norbert-walter/LoRa-Boat-Monitor/project/apps/pictures/Bonjour_Browser.png

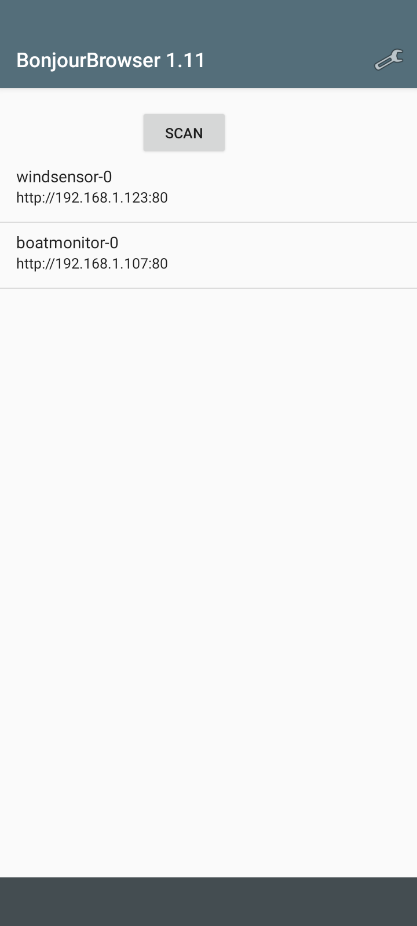
project/apps/pictures/Bonjour_Browser.png
