norbert-walter/LoRa-Boat-Monitor/project/apps/pictures/Lora_Info.png

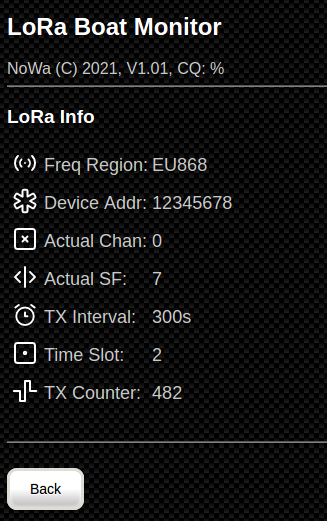
project/apps/pictures/Lora_Info.png
