norbert-walter/LoRa-Boat-Monitor/project/apps/pictures/Menue.png

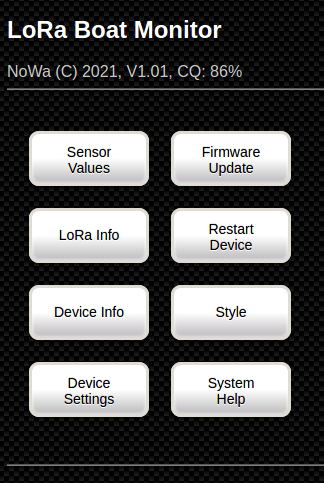
project/apps/pictures/Menue.png
