norbert-walter/LoRa-Boat-Monitor/project/apps/pictures/Screenshot_1.png

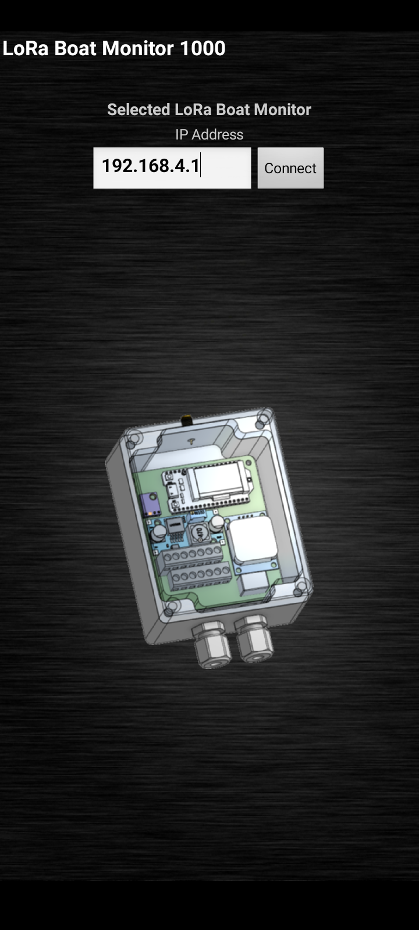
project/apps/pictures/Screenshot_1.png
