norbert-walter/LoRa-Boat-Monitor/project/apps/pictures/Screenshot_2.png

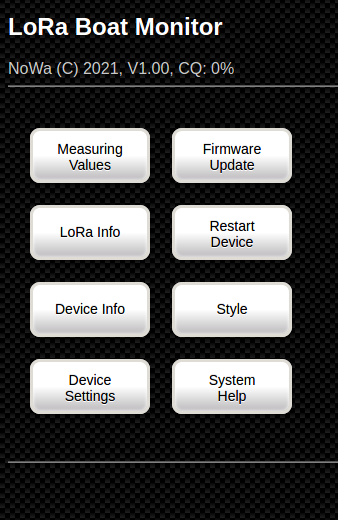
project/apps/pictures/Screenshot_2.png
