norbert-walter/LoRa-Boat-Monitor/project/apps/pictures/Sensor_Values1.png

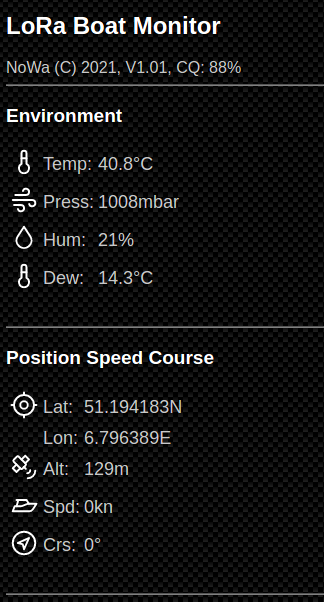
project/apps/pictures/Sensor_Values1.png
