norbert-walter/LoRa-Boat-Monitor/project/apps/pictures/Sensor_Values2.png

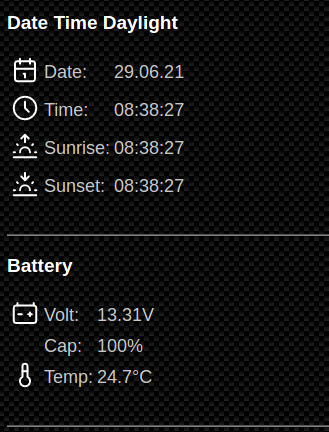
project/apps/pictures/Sensor_Values2.png
