norbert-walter/LoRa-Boat-Monitor/project/apps/pictures/Sensor_Values3.png

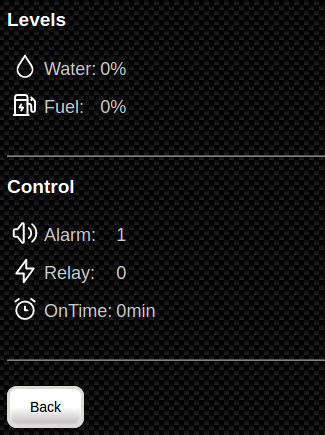
project/apps/pictures/Sensor_Values3.png
