norbert-walter/LoRa-Boat-Monitor/project/docs/Certifications/Heltec_LoRa32/464_Smith.png

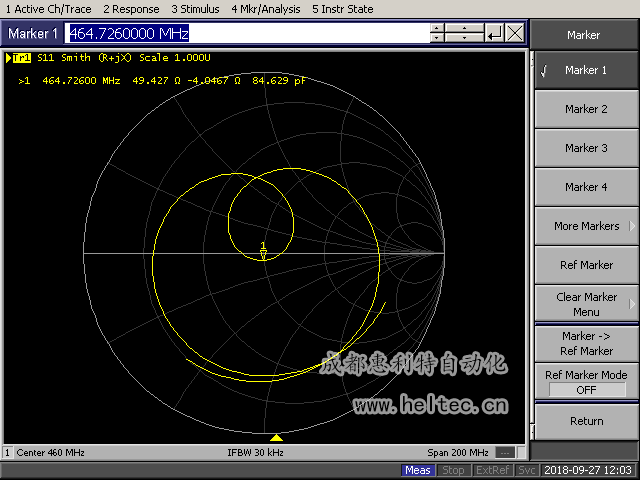
project/docs/Certifications/Heltec_LoRa32/464_Smith.png
