norbert-walter/LoRa-Boat-Monitor/project/docs/Certifications/Heltec_LoRa32/lite470.png

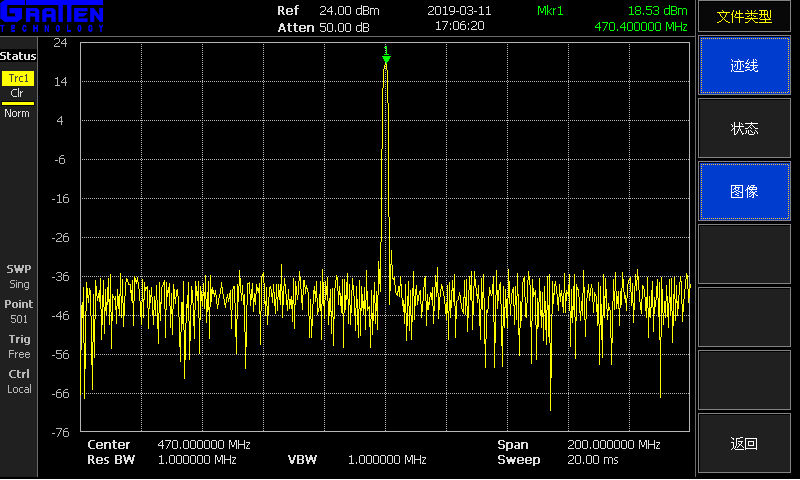
project/docs/Certifications/Heltec_LoRa32/lite470.png
