norbert-walter/LoRa-Boat-Monitor/project/docs/Certifications/Heltec_LoRa32/lite826.png

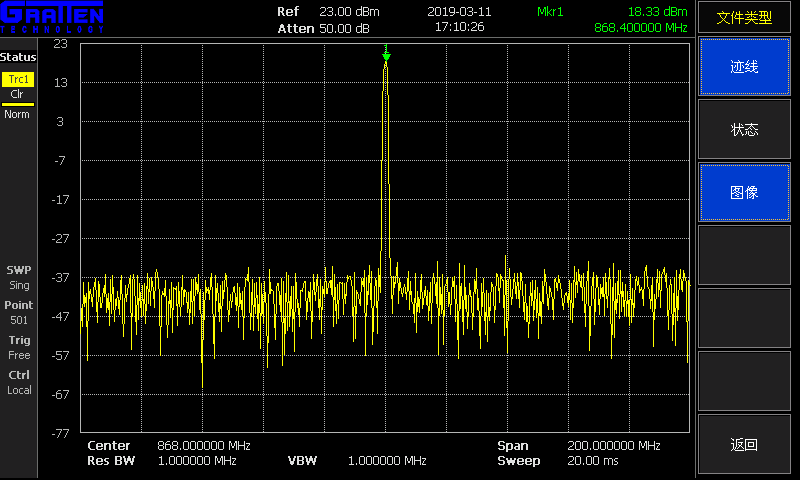
project/docs/Certifications/Heltec_LoRa32/lite826.png
