norbert-walter/LoRa-Boat-Monitor/project/docs/Certifications/Heltec_LoRa32/lite915.png

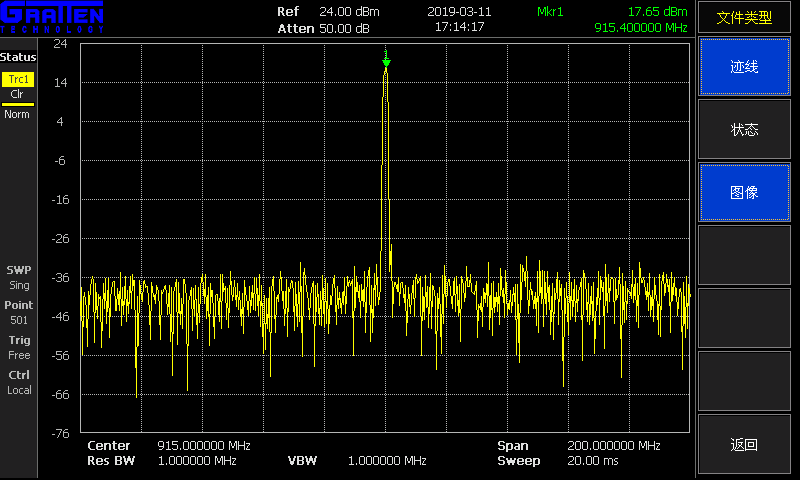
project/docs/Certifications/Heltec_LoRa32/lite915.png
