norbert-walter/LoRa-Boat-Monitor/project/docs/Componets/Heltec_WiFi_LoRa_32.png

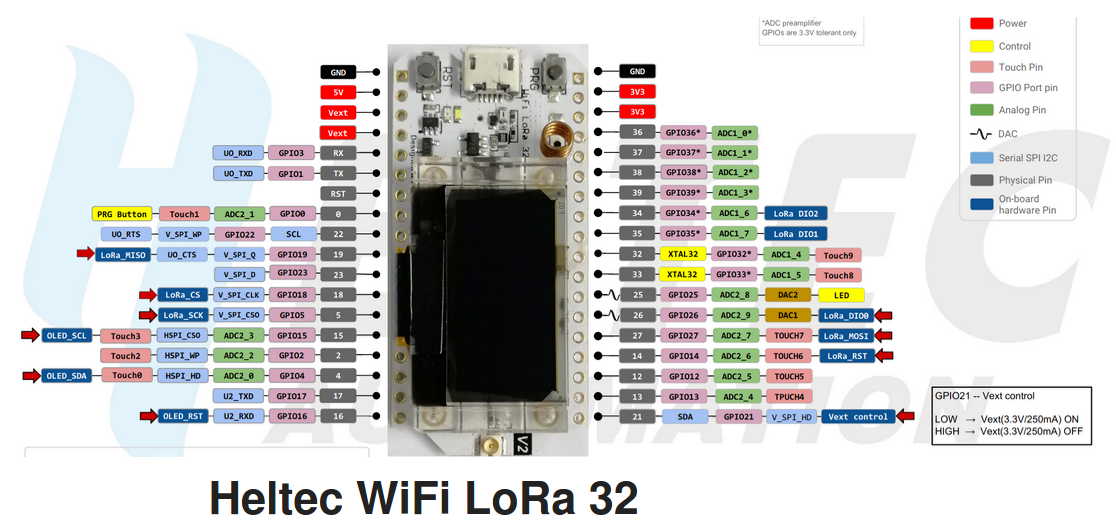
project/docs/Componets/Heltec_WiFi_LoRa_32.png
