norbert-walter/LoRa-Boat-Monitor/project/pictures/LoRa_Boat_Monitor/Füllstandssensor_180_Ohm.jpg

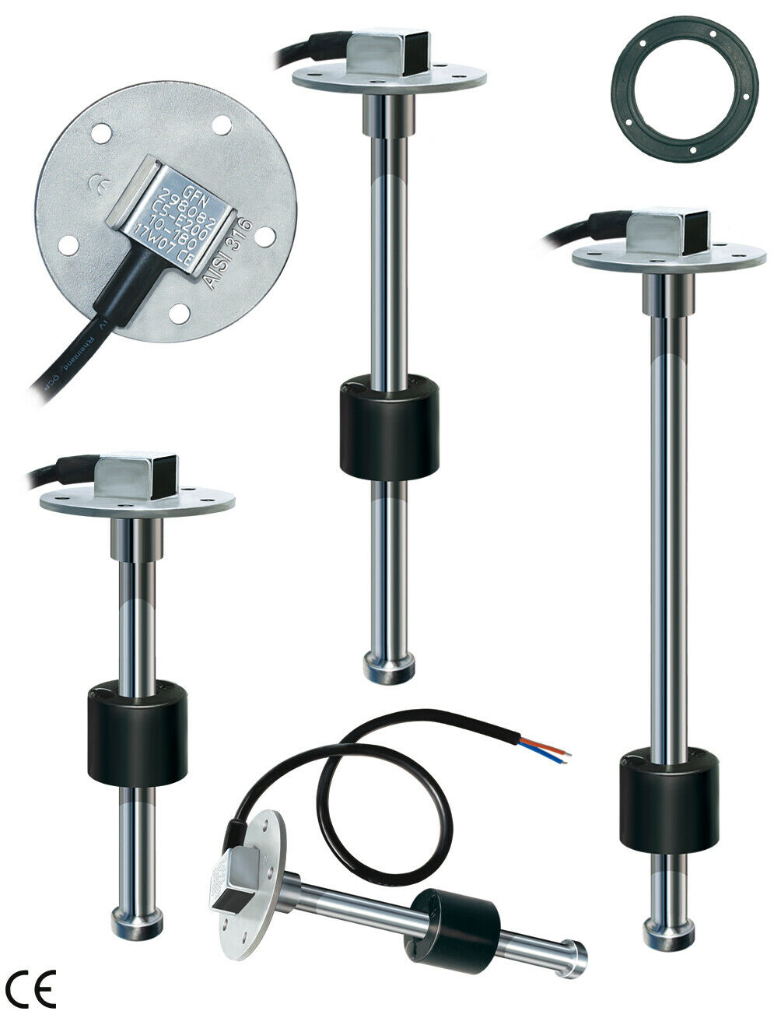
project/pictures/LoRa_Boat_Monitor/Füllstandssensor_180_Ohm.jpg
