norbert-walter/LoRa-Boat-Monitor/project/pictures/LoRa_Boat_Monitor/IMG_20200325_182847_kl.jpg

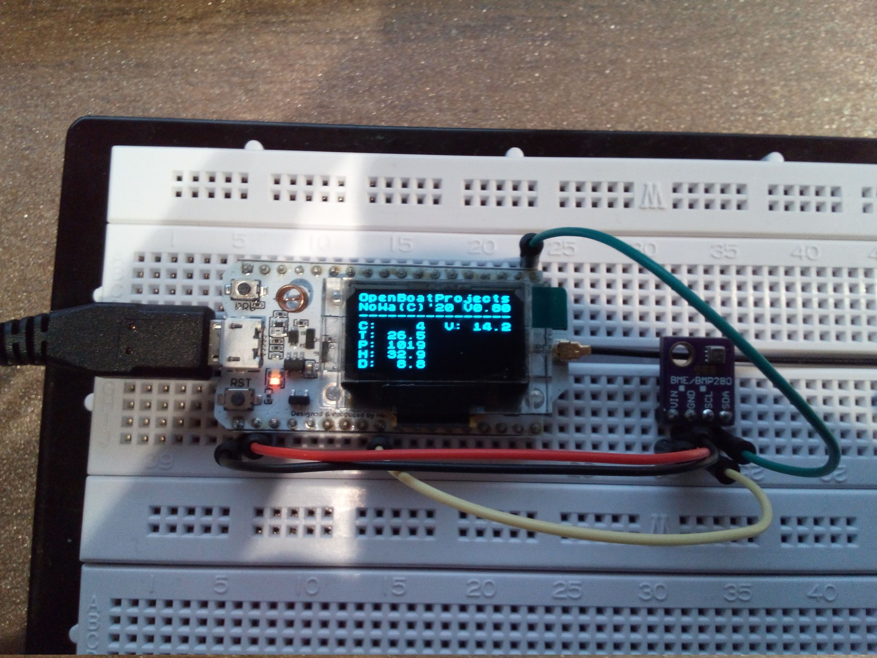
project/pictures/LoRa_Boat_Monitor/IMG_20200325_182847_kl.jpg
