norbert-walter/LoRa-Boat-Monitor/project/pictures/LoRa_Boat_Monitor/IMG_20200403_091831_kl.jpg

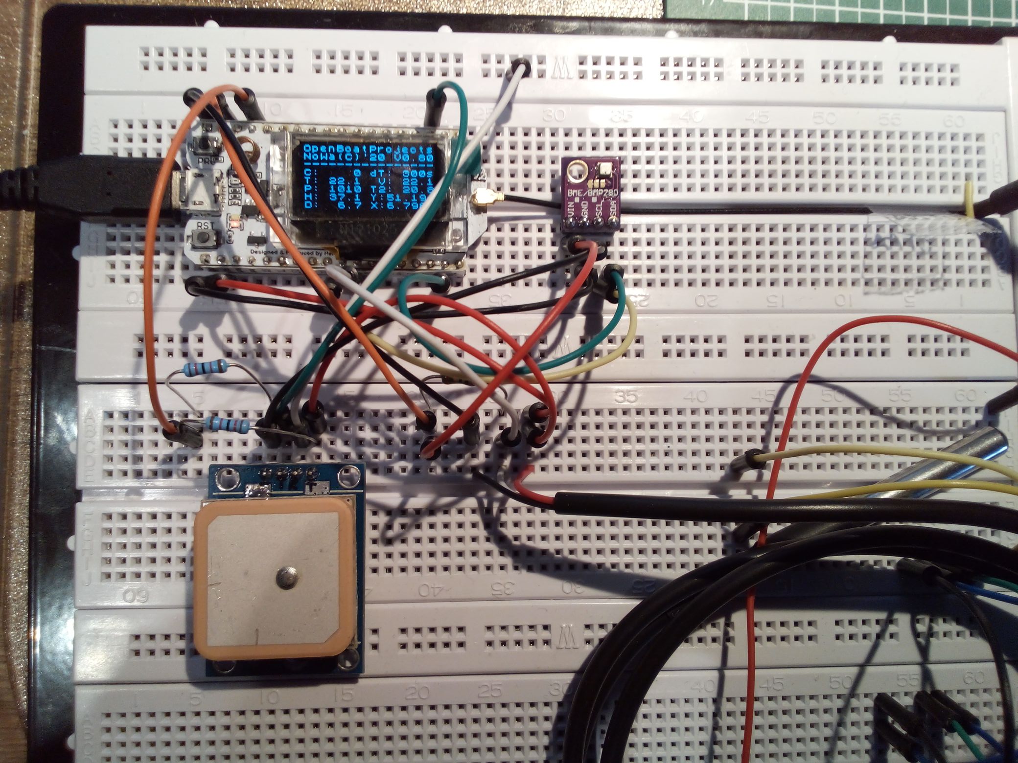
project/pictures/LoRa_Boat_Monitor/IMG_20200403_091831_kl.jpg
