norbert-walter/LoRa-Boat-Monitor/project/pictures/LoRa_Boat_Monitor/IMG_20200506_172737_kl.jpg

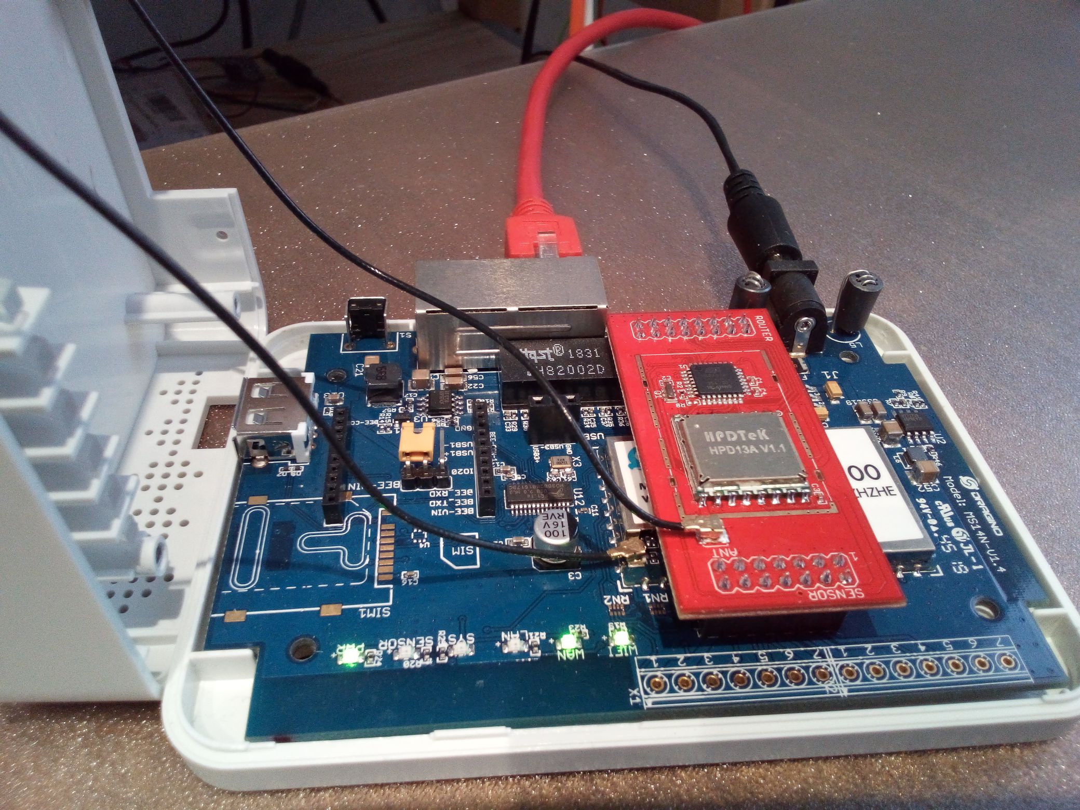
project/pictures/LoRa_Boat_Monitor/IMG_20200506_172737_kl.jpg
