norbert-walter/LoRa-Boat-Monitor/project/pictures/LoRa_Boat_Monitor/IMG_20200603_171321_kl.jpg

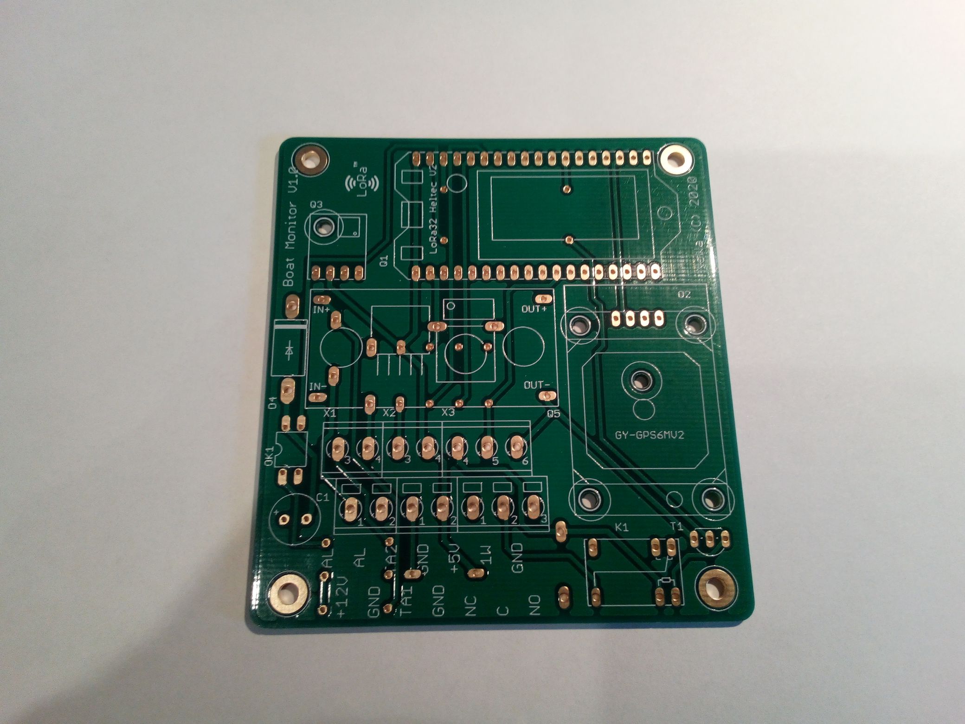
project/pictures/LoRa_Boat_Monitor/IMG_20200603_171321_kl.jpg
