norbert-walter/LoRa-Boat-Monitor/project/pictures/LoRa_Boat_Monitor/IMG_20200603_210354_kl.jpg

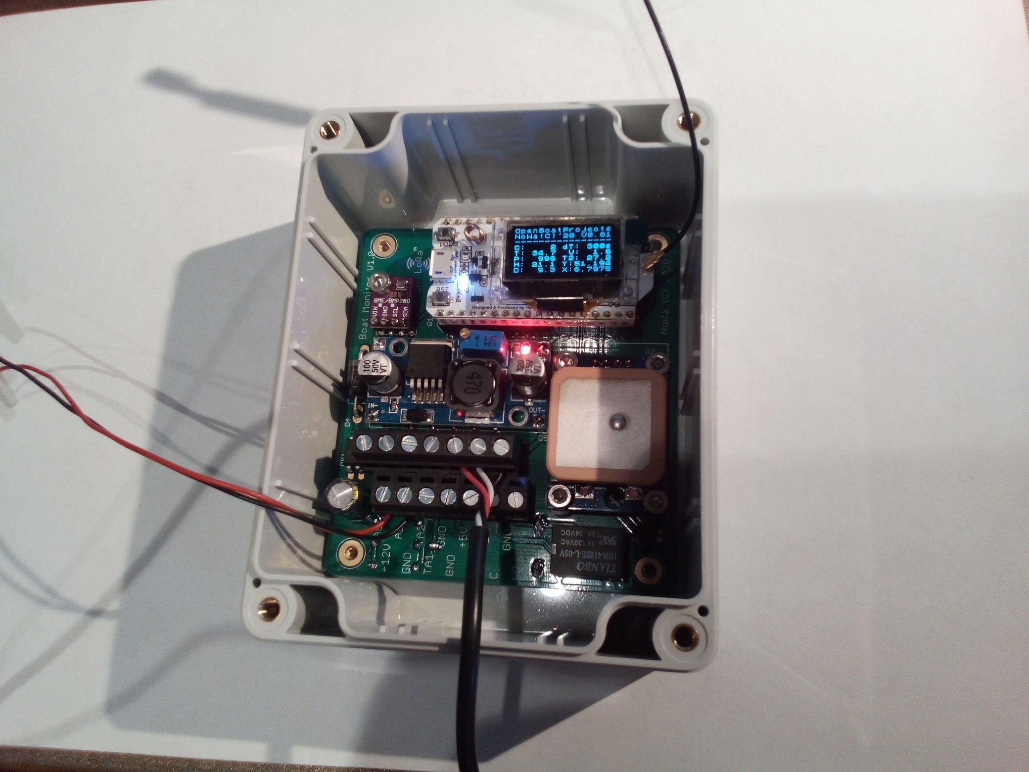
project/pictures/LoRa_Boat_Monitor/IMG_20200603_210354_kl.jpg
