norbert-walter/LoRa-Boat-Monitor/project/pictures/LoRa_Boat_Monitor/IMG_20200605_140513_kl.jpg

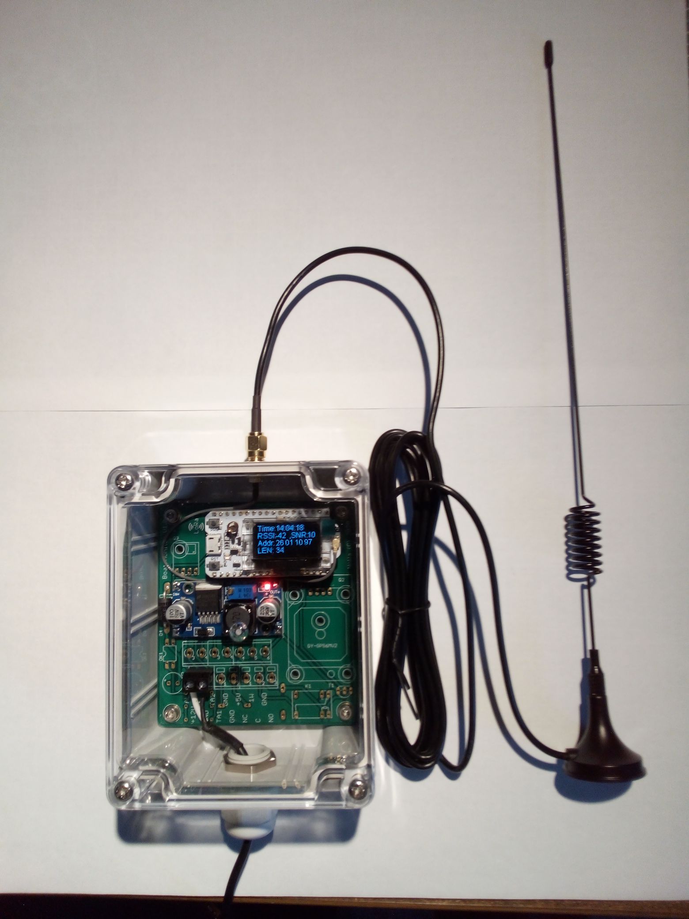
project/pictures/LoRa_Boat_Monitor/IMG_20200605_140513_kl.jpg
