norbert-walter/LoRa-Boat-Monitor/project/pictures/LoRa_Boat_Monitor/IMG_20201030_144952_kl.jpg

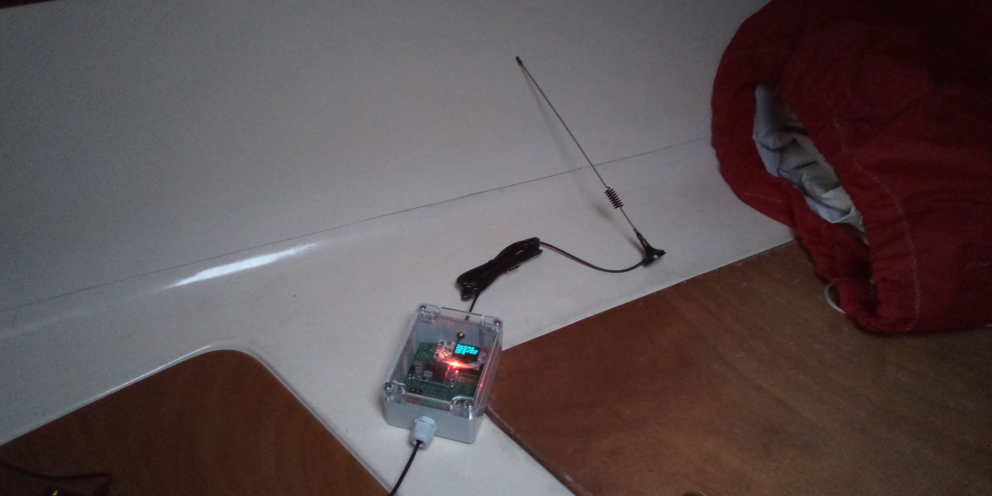
project/pictures/LoRa_Boat_Monitor/IMG_20201030_144952_kl.jpg
