norbert-walter/LoRa-Boat-Monitor/project/pictures/LoRa_Boat_Monitor/IMG_20210512_152236_kl.jpg

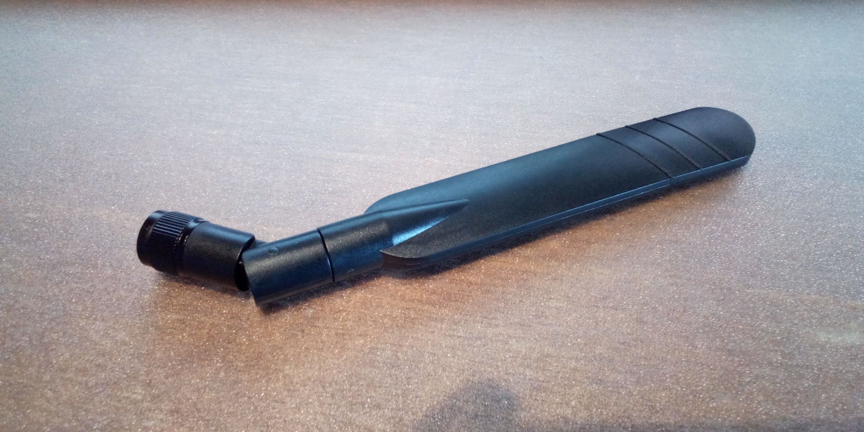
project/pictures/LoRa_Boat_Monitor/IMG_20210512_152236_kl.jpg
