norbert-walter/LoRa-Boat-Monitor/project/pictures/LoRa_Boat_Monitor/IMG_20210512_152258_kl.jpg

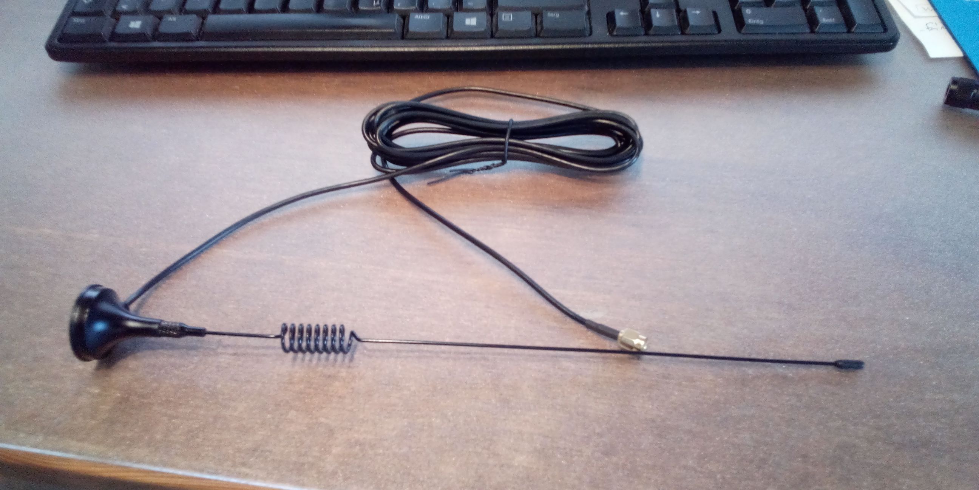
project/pictures/LoRa_Boat_Monitor/IMG_20210512_152258_kl.jpg
