norbert-walter/LoRa-Boat-Monitor/project/pictures/LoRa_Boat_Monitor/LoRa-Frequenz-und-Signalstärke_klein_klein.jpg

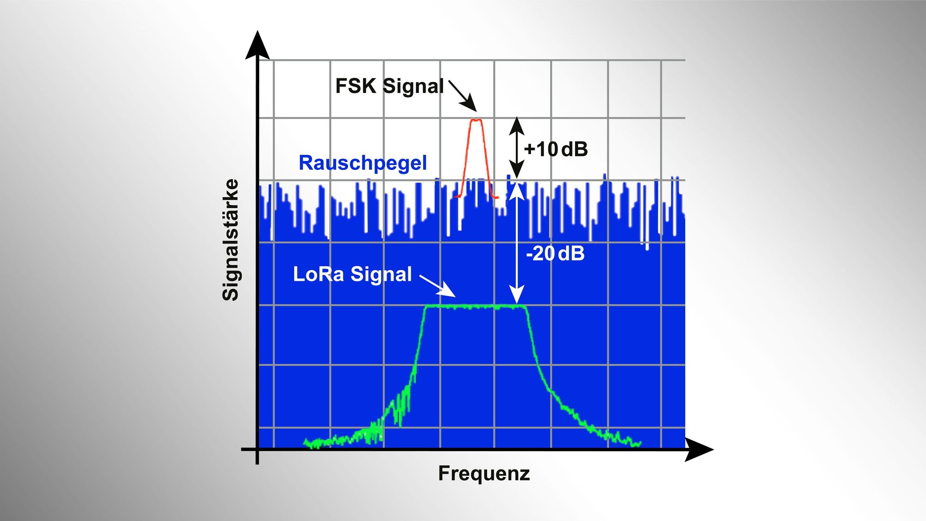
project/pictures/LoRa_Boat_Monitor/LoRa-Frequenz-und-Signalstärke_klein_klein.jpg
