norbert-walter/LoRa-Boat-Monitor/project/pictures/LoRa_Boat_Monitor/LoRa_Boatmonitor_Case.png

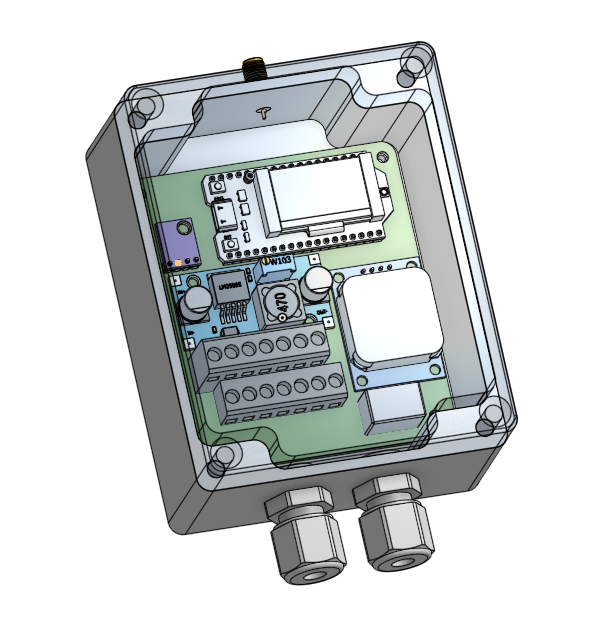
project/pictures/LoRa_Boat_Monitor/LoRa_Boatmonitor_Case.png
