norbert-walter/LoRa-Boat-Monitor/project/pictures/LoRa_Boat_Monitor/LoRa_Boots_Monitor_2.png

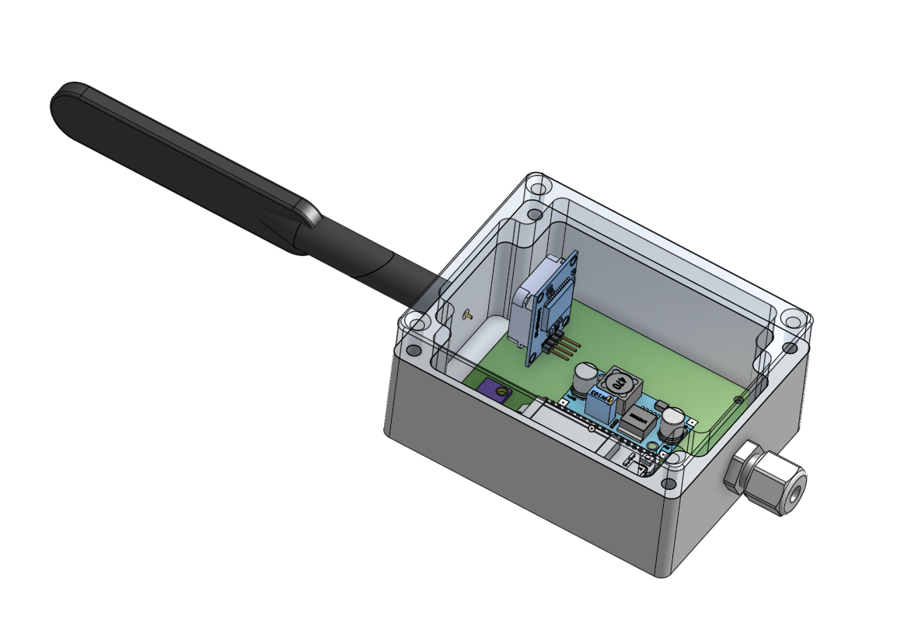
project/pictures/LoRa_Boat_Monitor/LoRa_Boots_Monitor_2.png
