norbert-walter/LoRa-Boat-Monitor/project/pictures/LoRa_Boat_Monitor/LoRa_Bootsmonitor.png

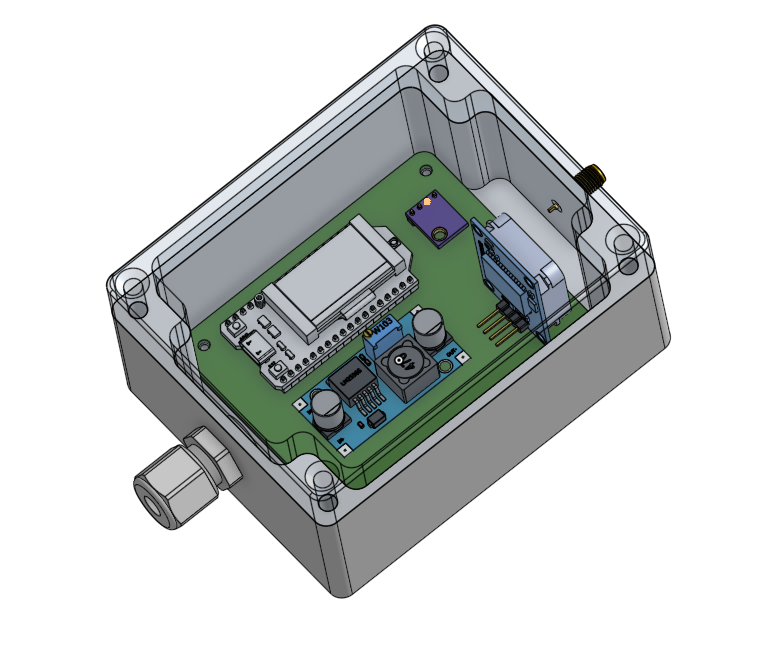
project/pictures/LoRa_Boat_Monitor/LoRa_Bootsmonitor.png
