norbert-walter/LoRa-Boat-Monitor/project/pictures/LoRa_Boat_Monitor/LoRa_Bootsmonitor_Bottom_2_kl.png

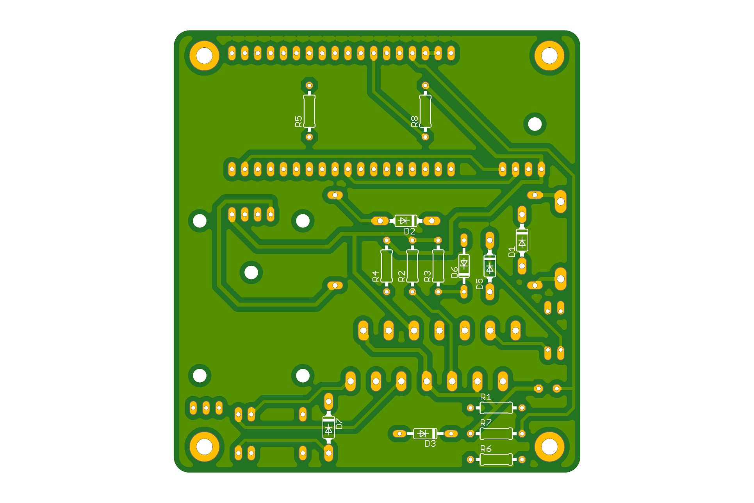
project/pictures/LoRa_Boat_Monitor/LoRa_Bootsmonitor_Bottom_2_kl.png
