norbert-walter/LoRa-Boat-Monitor/project/pictures/LoRa_Boat_Monitor/LoRa_Bootsmonitor_Top_2_kl.png

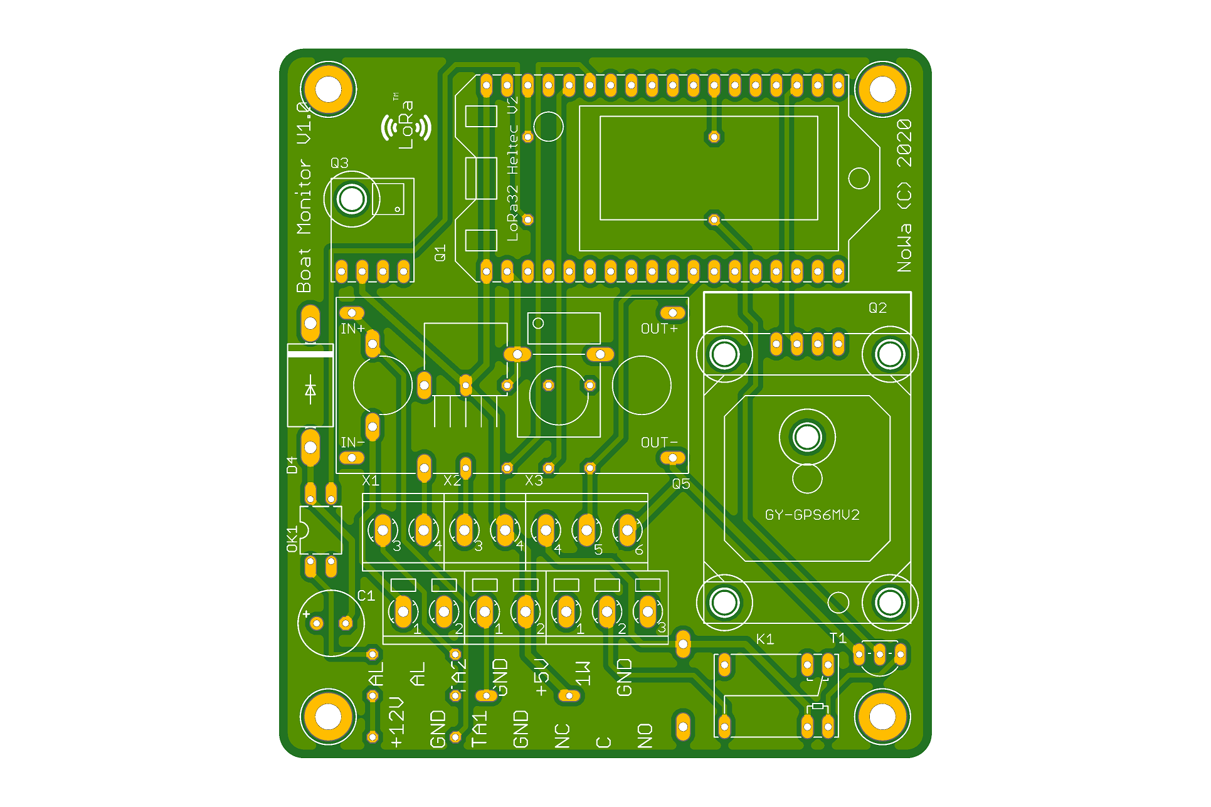
project/pictures/LoRa_Boat_Monitor/LoRa_Bootsmonitor_Top_2_kl.png
