norbert-walter/LoRa-Boat-Monitor/project/pictures/LoRa_Boat_Monitor/Schwimmschalter.jpg

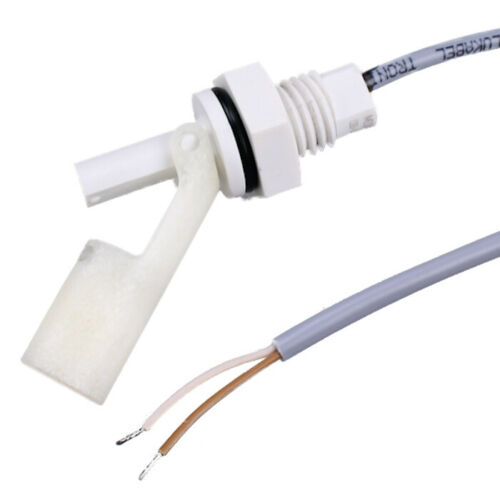
project/pictures/LoRa_Boat_Monitor/Schwimmschalter.jpg
