norbert-walter/LoRa-Boat-Monitor/project/pictures/LoRa_Boat_Monitor/Schwimmschalter_3.jpg

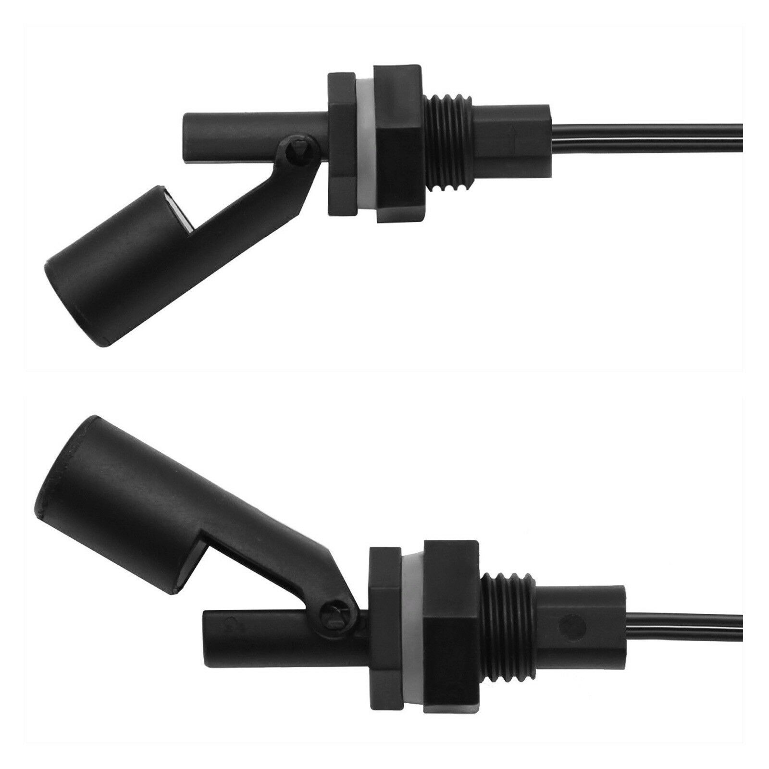
project/pictures/LoRa_Boat_Monitor/Schwimmschalter_3.jpg
