norbert-walter/LoRa-Boat-Monitor/project/pictures/LoRa_Boat_Monitor/Türschalter_magnetisch.jpg

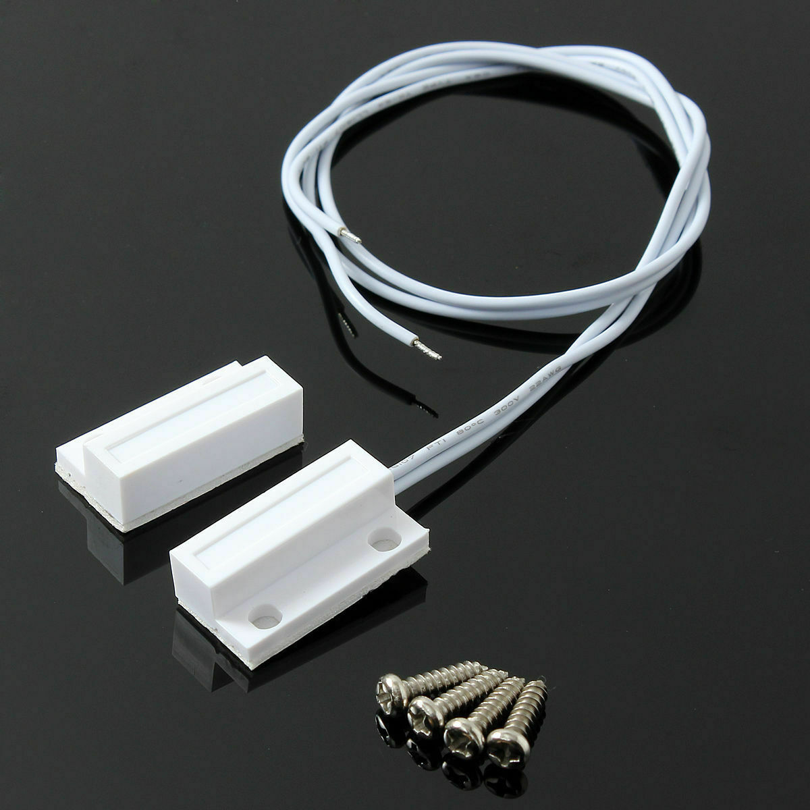
project/pictures/LoRa_Boat_Monitor/Türschalter_magnetisch.jpg
