norbert-walter/LoRa-Boat-Monitor/project/pictures/LoRa_Gateway/Dragino_LoRa_Gateway_LG01-P.png

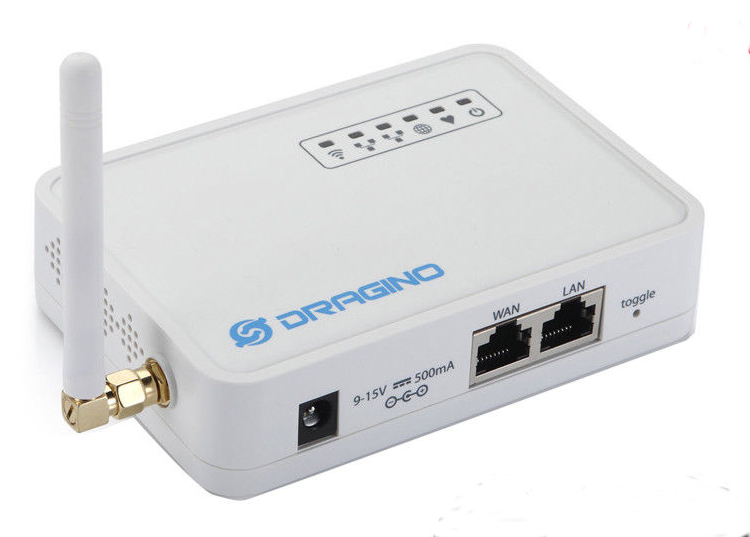
project/pictures/LoRa_Gateway/Dragino_LoRa_Gateway_LG01-P.png
