norbert-walter/LoRa-Boat-Monitor/project/pictures/LoRa_Gateway/LoRa_1Ch_Gateway.png

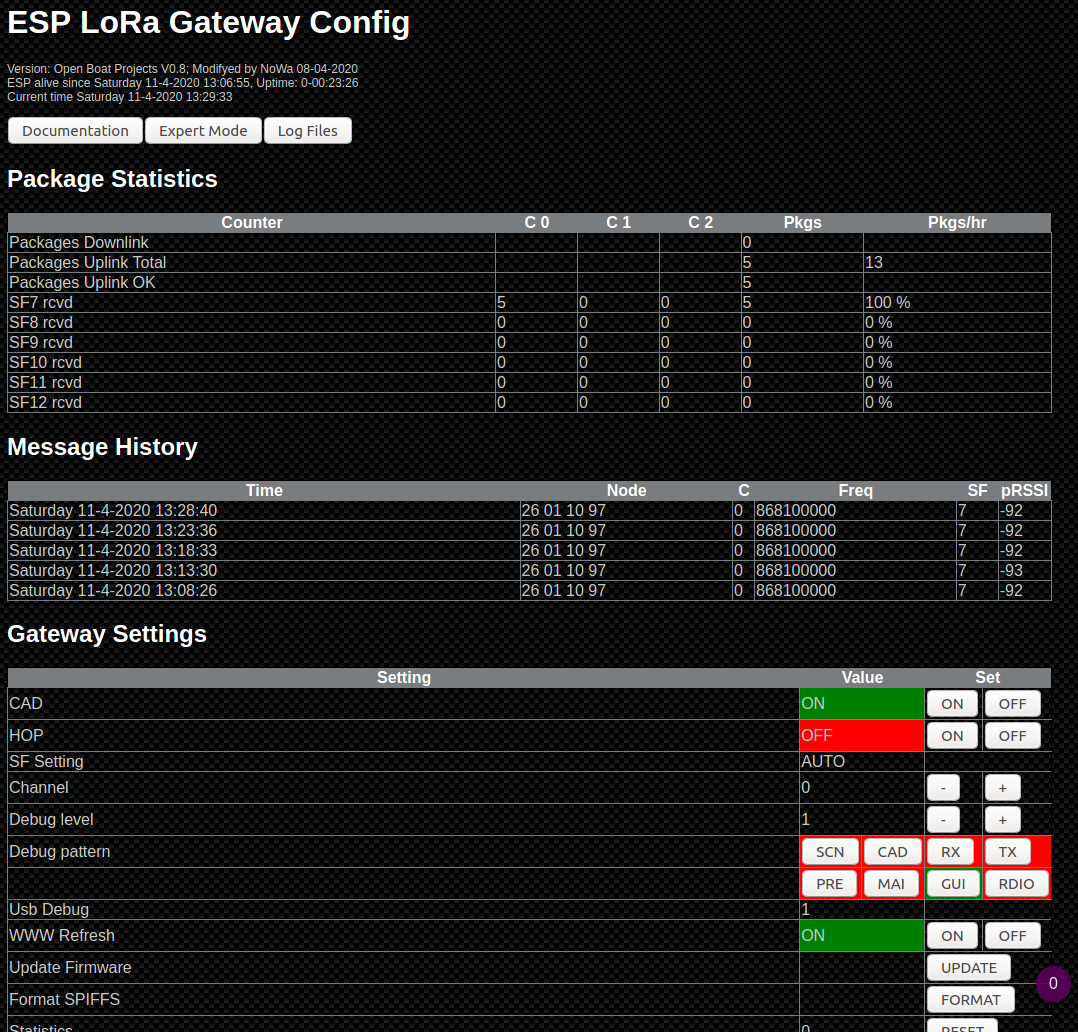
project/pictures/LoRa_Gateway/LoRa_1Ch_Gateway.png
