norbert-walter/LoRa-Boat-Monitor/project/pictures/LoRa_Gateway/LoRa_Gateway.png

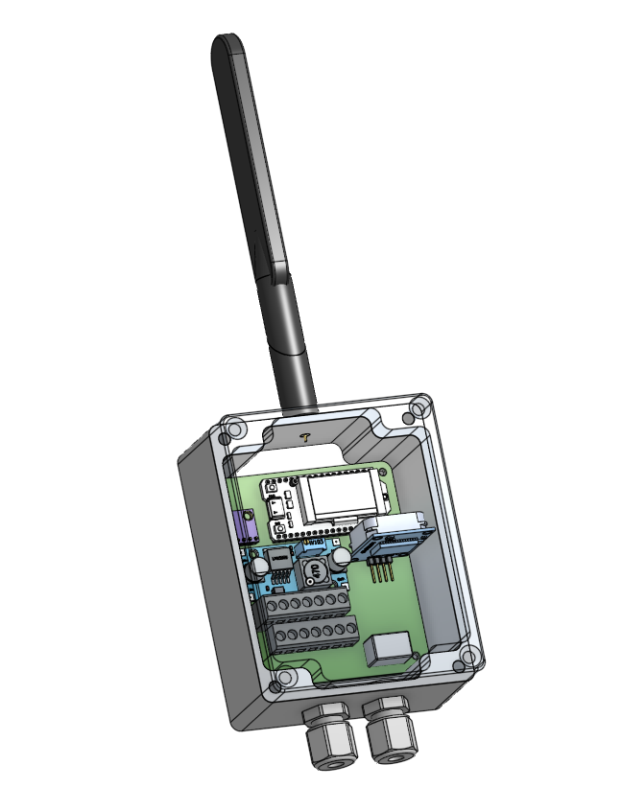
project/pictures/LoRa_Gateway/LoRa_Gateway.png
