norbert-walter/LoRa-Boat-Monitor/project/pictures/Sailboat_bl_or.png

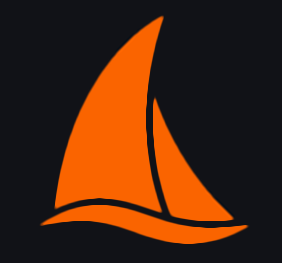
project/pictures/Sailboat_bl_or.png
