norbert-walter/LoRa-Boat-Monitor/project/pictures/TTN/Application_Data.png

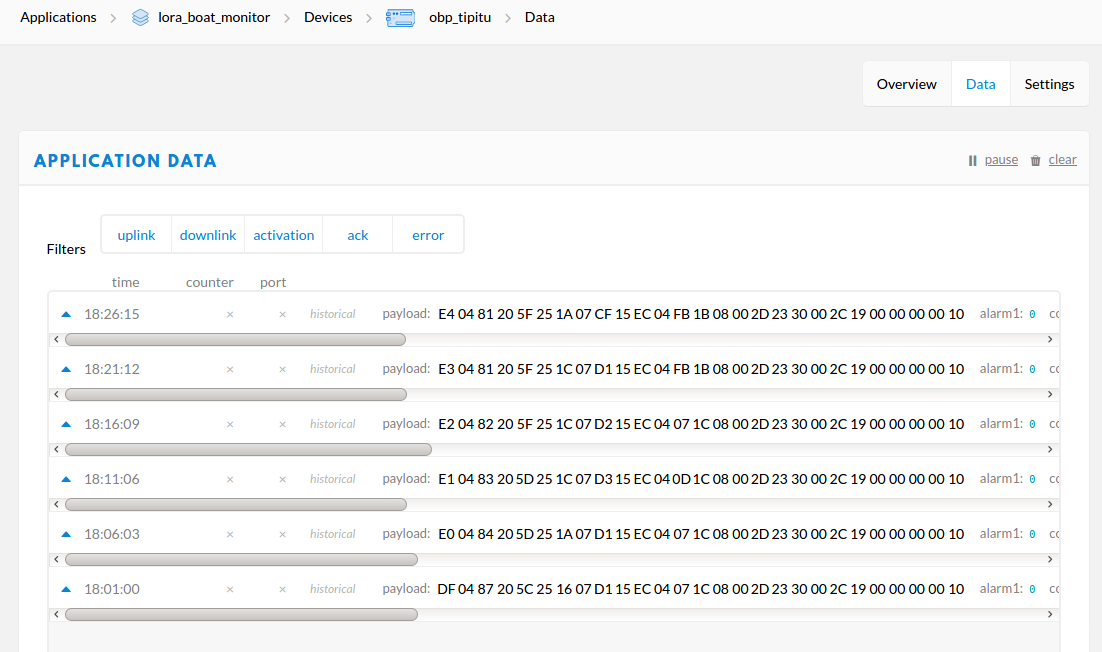
project/pictures/TTN/Application_Data.png
