norbert-walter/LoRa-Boat-Monitor/project/pictures/TTN/Metadata.png

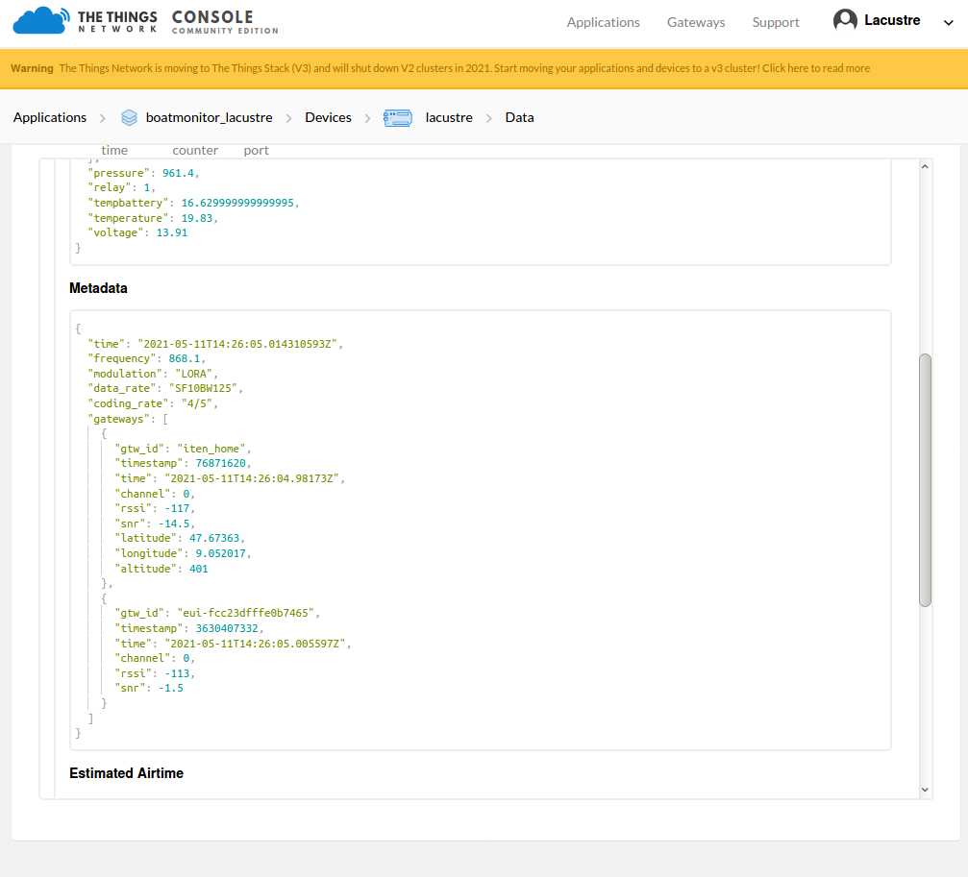
project/pictures/TTN/Metadata.png
