norbert-walter/LoRa-Boat-Monitor/project/pictures/TTN/Upload_Bestaetigung2.png

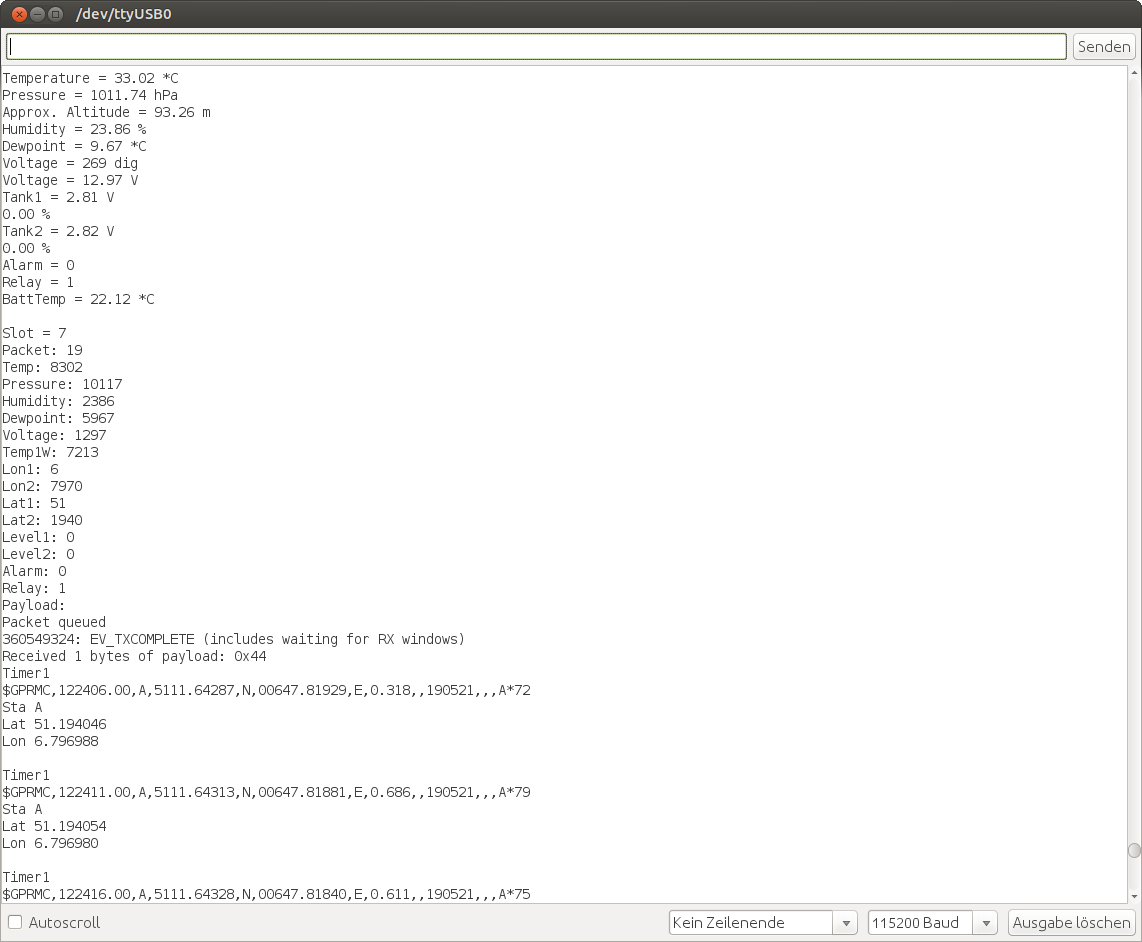
project/pictures/TTN/Upload_Bestaetigung2.png
