norbert-walter/LoRa-Boat-Monitor/project/pictures/TTN/Upload_Bestaetigung.png

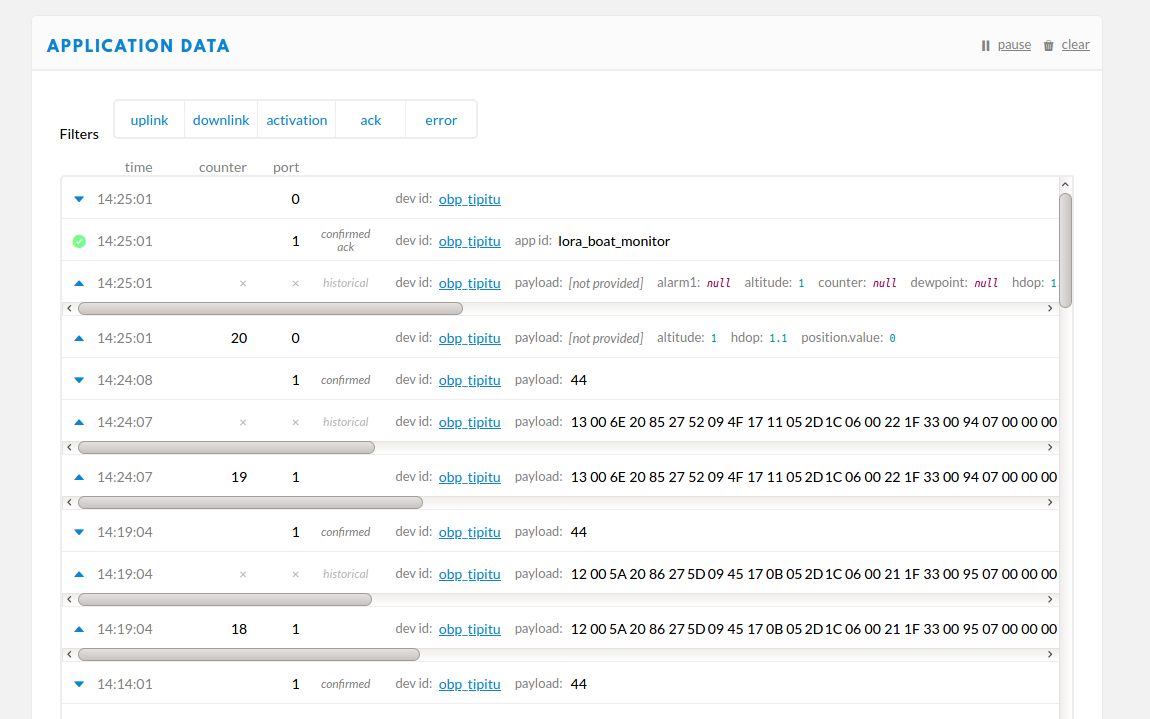
project/pictures/TTN/Upload_Bestaetigung.png
