norbert-walter/LoRa-Boat-Monitor/project/pictures/Ubidots/LoRa_Monitoring_Karte.png

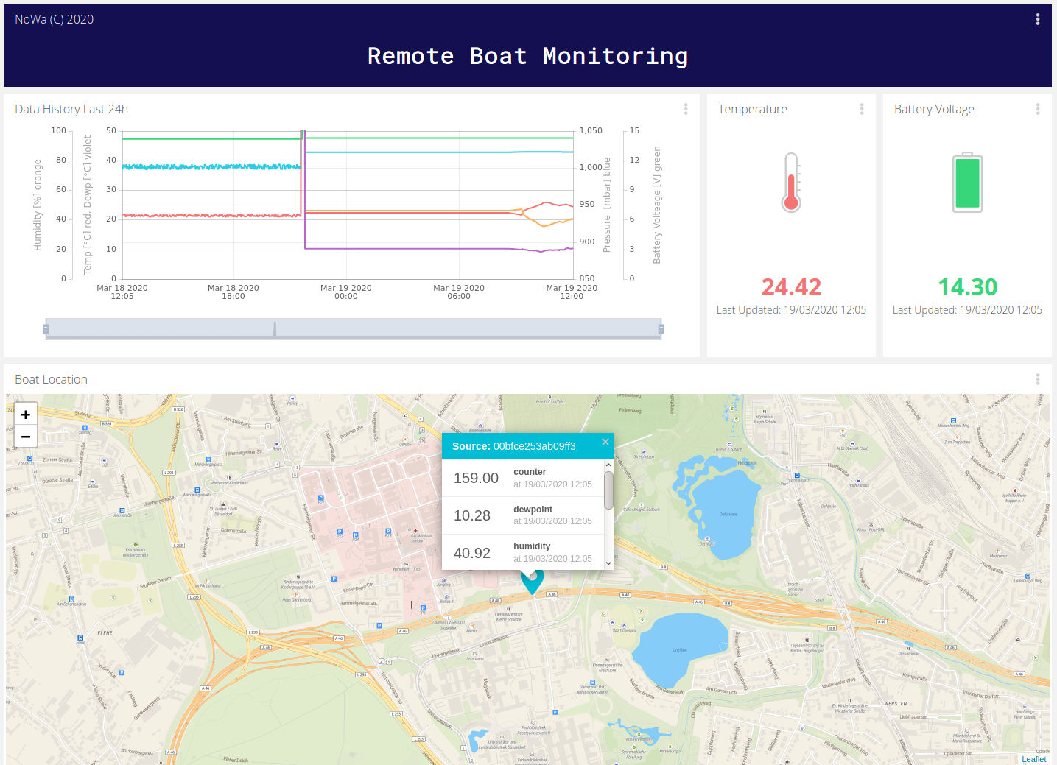
project/pictures/Ubidots/LoRa_Monitoring_Karte.png
