norbert-walter/LoRa-Boat-Monitor/project/pictures/Ubidots/SY-Balder Messdaten2.png

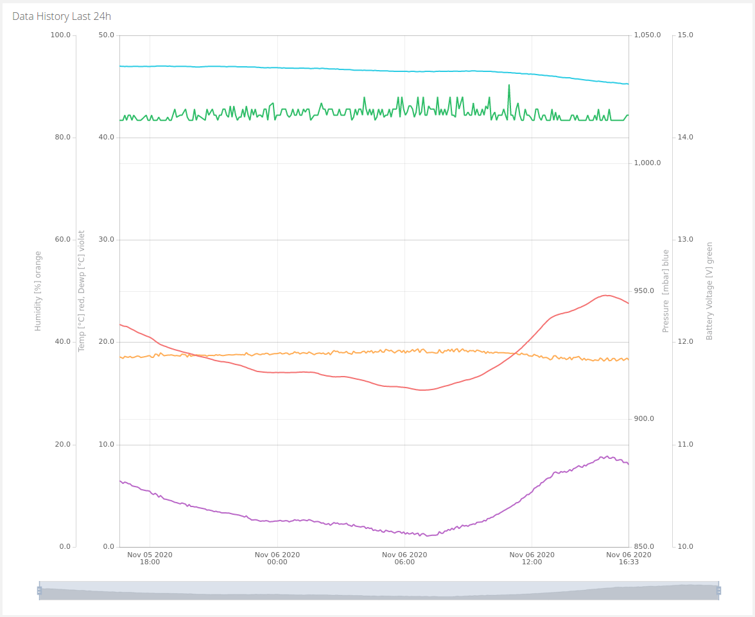
project/pictures/Ubidots/SY-Balder Messdaten2.png
