norbert-walter/LoRa-Boat-Monitor/project/pictures/Ubidots/SY-Balder_Messdaten.png

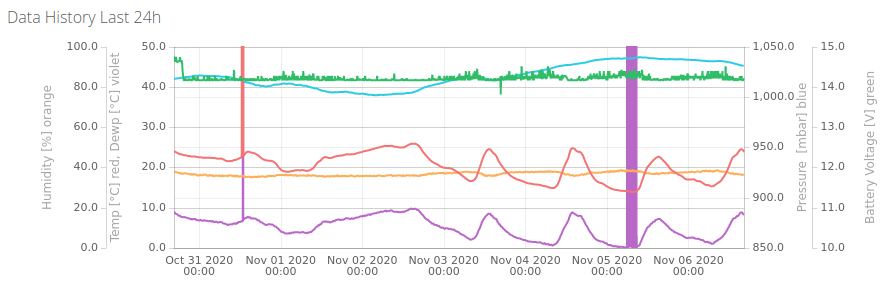
project/pictures/Ubidots/SY-Balder_Messdaten.png
