norbert-walter/LoRa-Boat-Monitor/project/pictures/Ubidots/Ubidots_24h_Verbindungsqualitaet.png

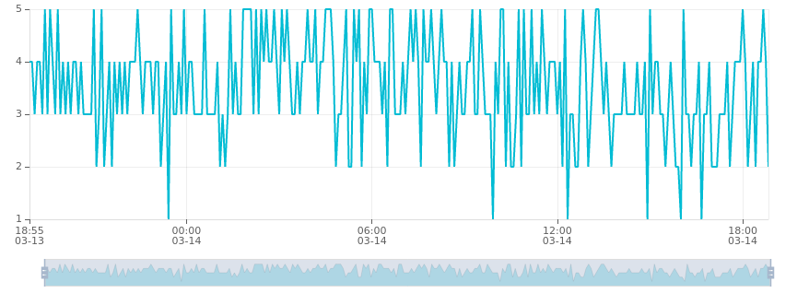
project/pictures/Ubidots/Ubidots_24h_Verbindungsqualitaet.png
