norbert-walter/LoRa-Boat-Monitor/project/pictures/Antenna_Characteristic/Knickantenne.png

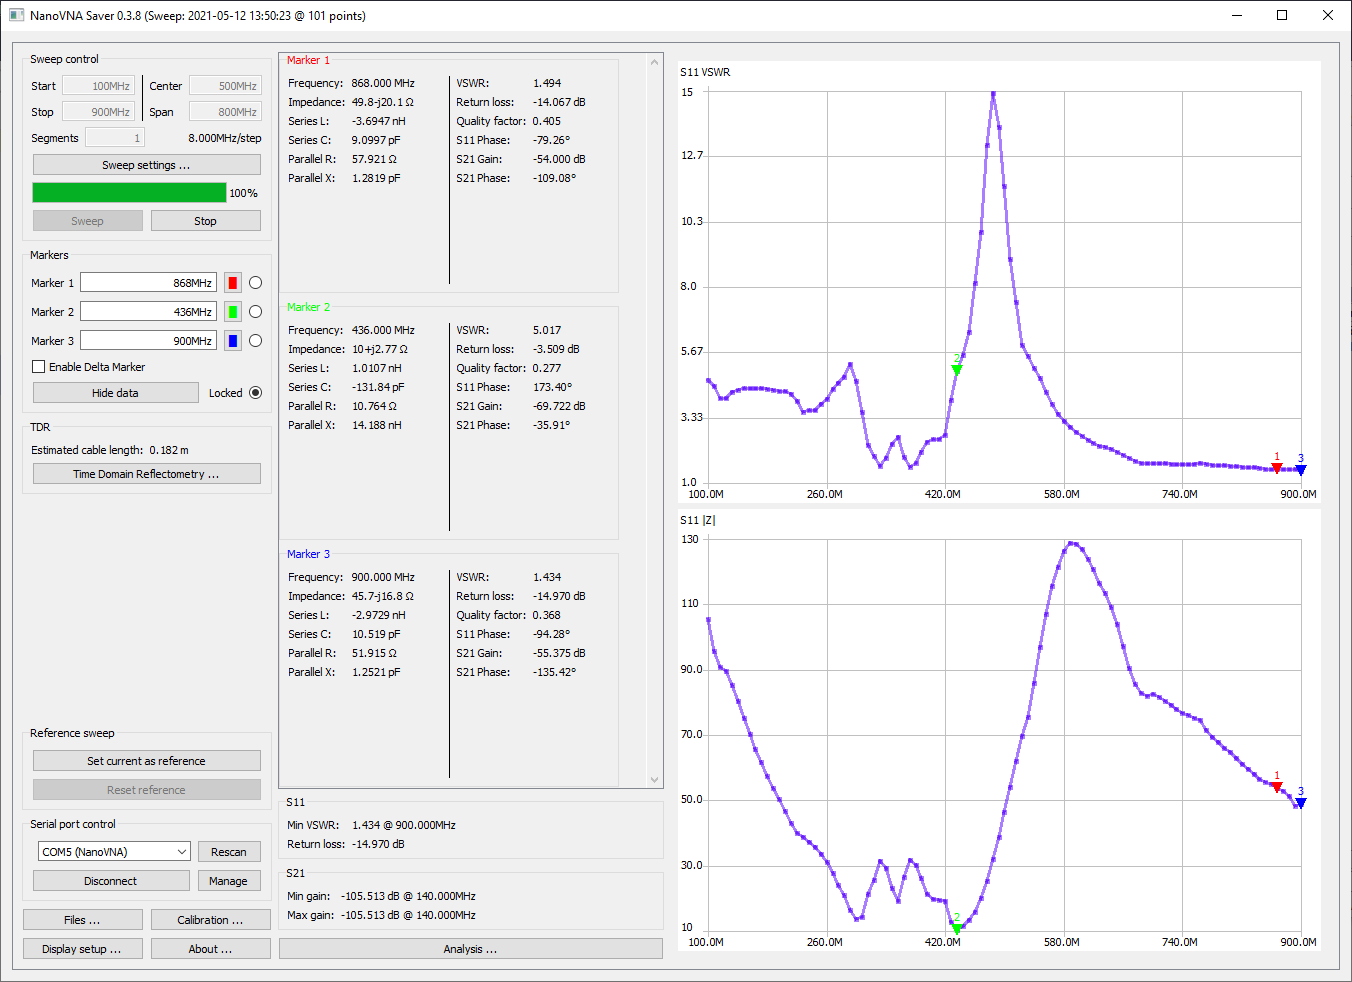
project/pictures/Antenna_Characteristic/Knickantenne.png
