norbert-walter/LoRa-Boat-Monitor/project/pictures/Antenna_Characteristic/NanoVNA.jpg

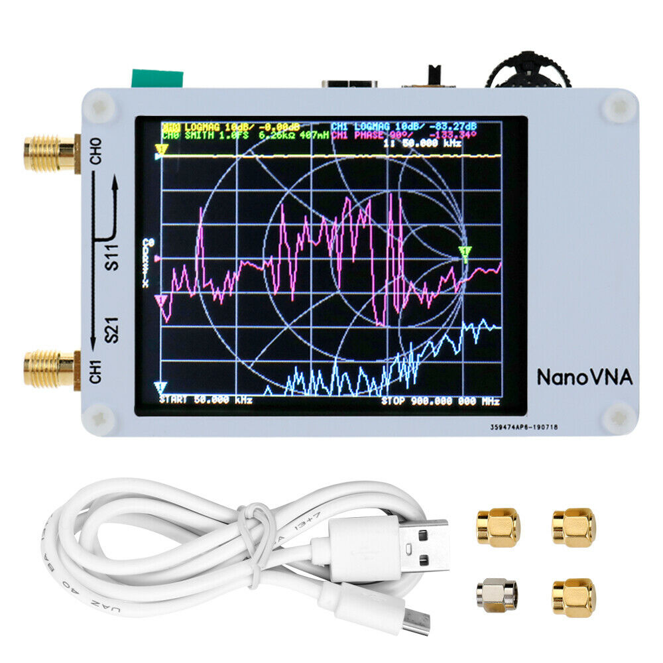
project/pictures/Antenna_Characteristic/NanoVNA.jpg
