norbert-walter/LoRa-Boat-Monitor/project/pictures/Antenna_Characteristic/Stababtenne_offenes_Ende.png

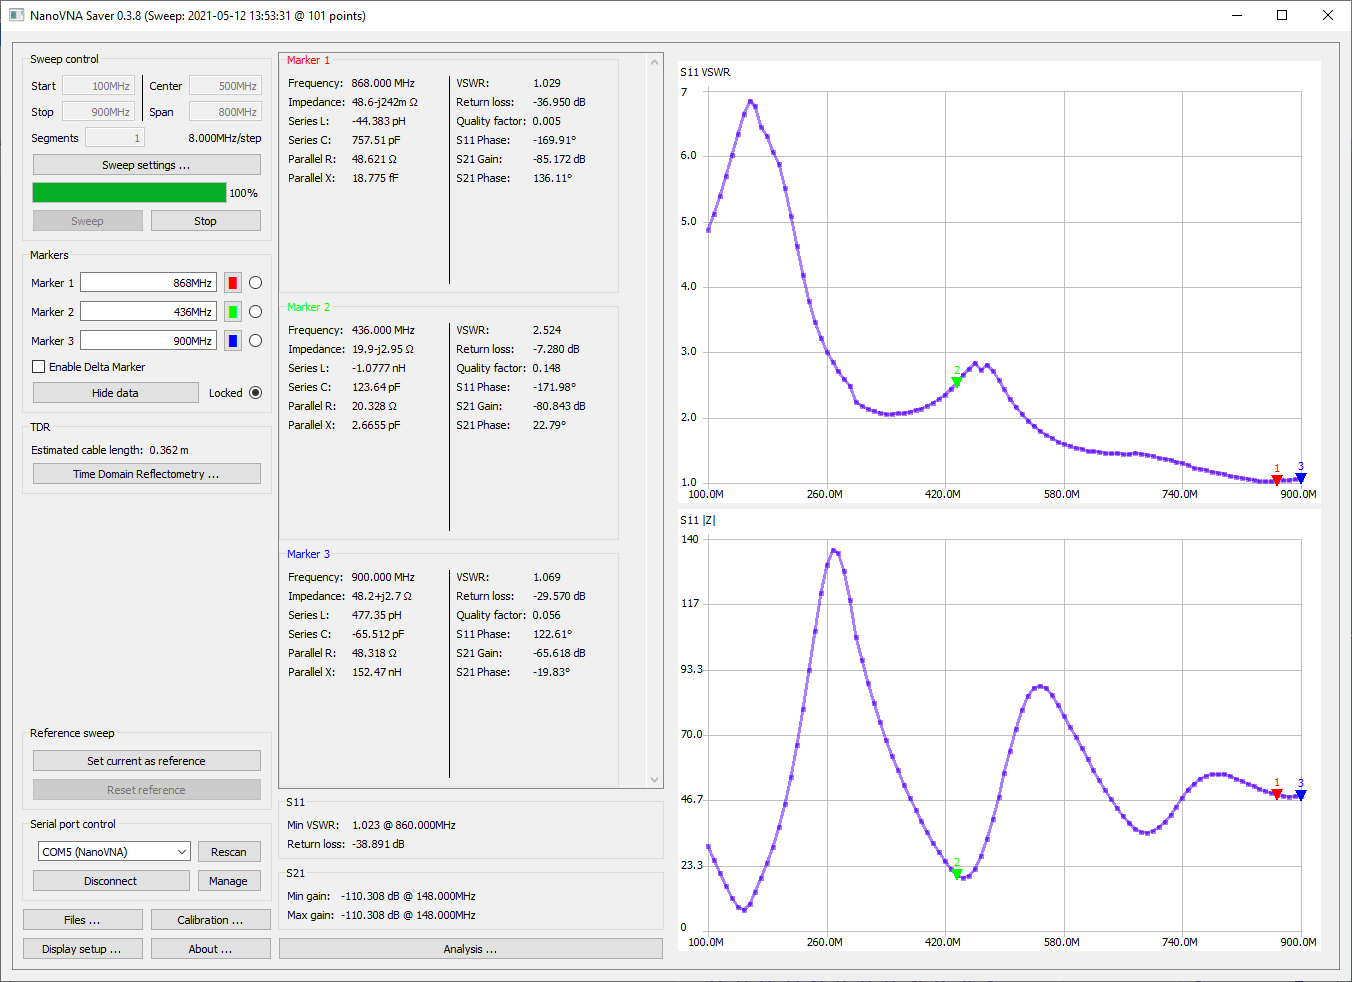
project/pictures/Antenna_Characteristic/Stababtenne_offenes_Ende.png
