norbert-walter/LoRa-Boat-Monitor/project/pictures/Range_Tests/Abdeckung_LoRa_IJssemeer.png

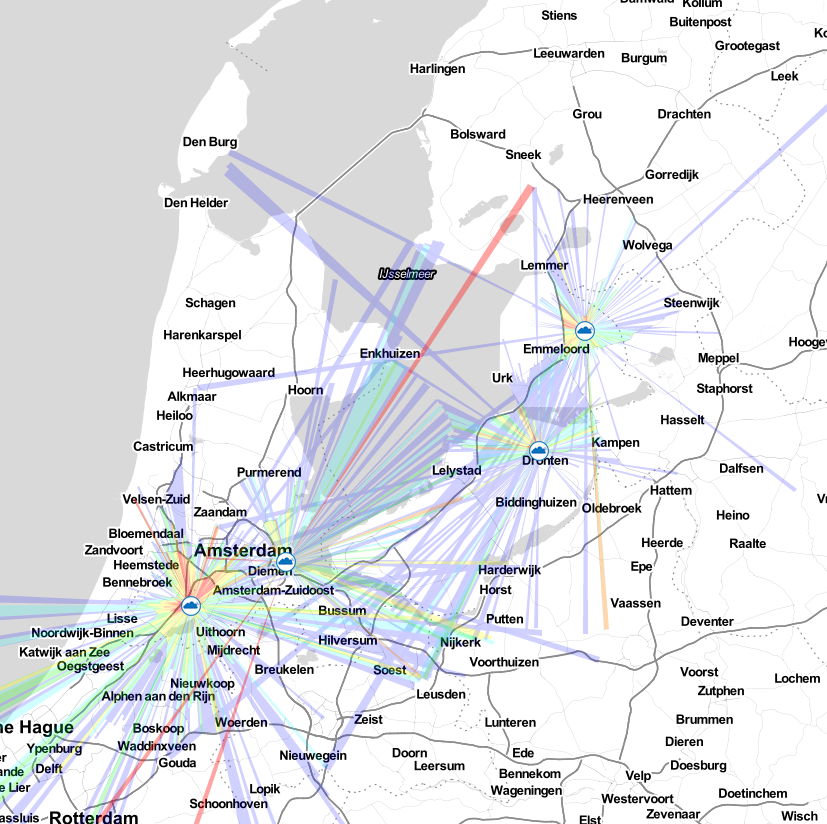
project/pictures/Range_Tests/Abdeckung_LoRa_IJssemeer.png
