norbert-walter/LoRa-Boat-Monitor/project/pictures/Range_Tests/Ausbreitungskarte.png

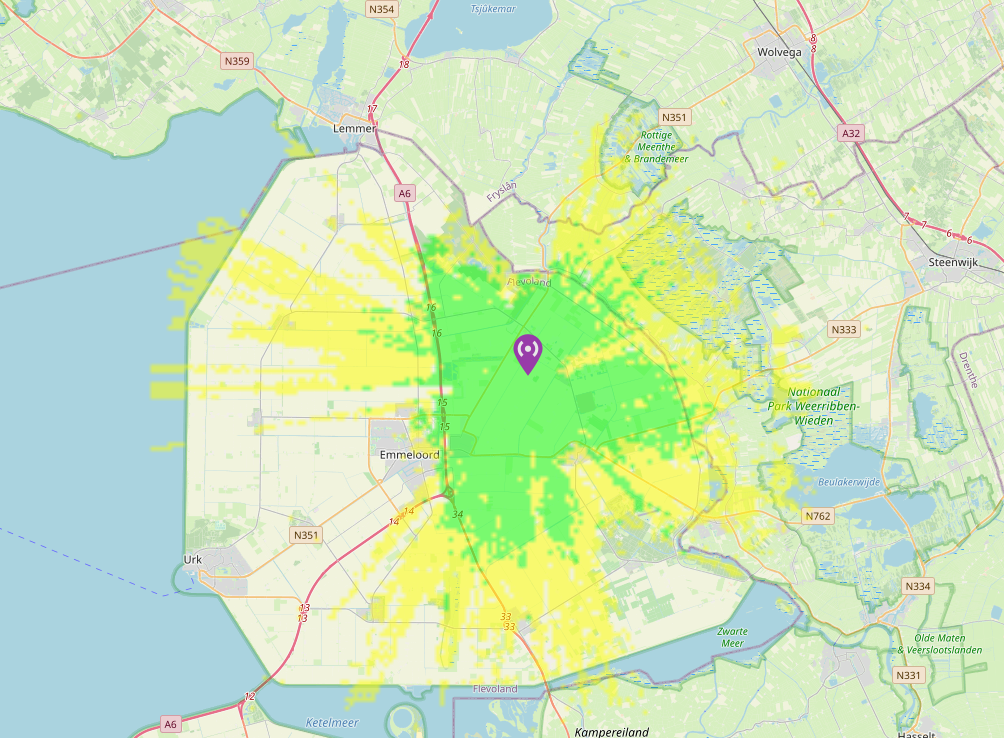
project/pictures/Range_Tests/Ausbreitungskarte.png
