norbert-walter/LoRa-Boat-Monitor/project/pictures/Range_Tests/Boot_Nussdorf_4.87km.jpg

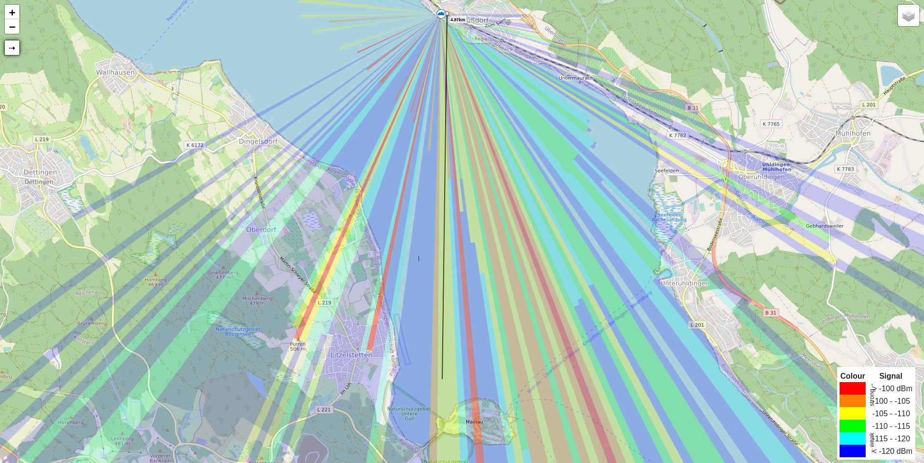
project/pictures/Range_Tests/Boot_Nussdorf_4.87km.jpg
