norbert-walter/LoRa-Boat-Monitor/project/pictures/Range_Tests/iten_home_2.png

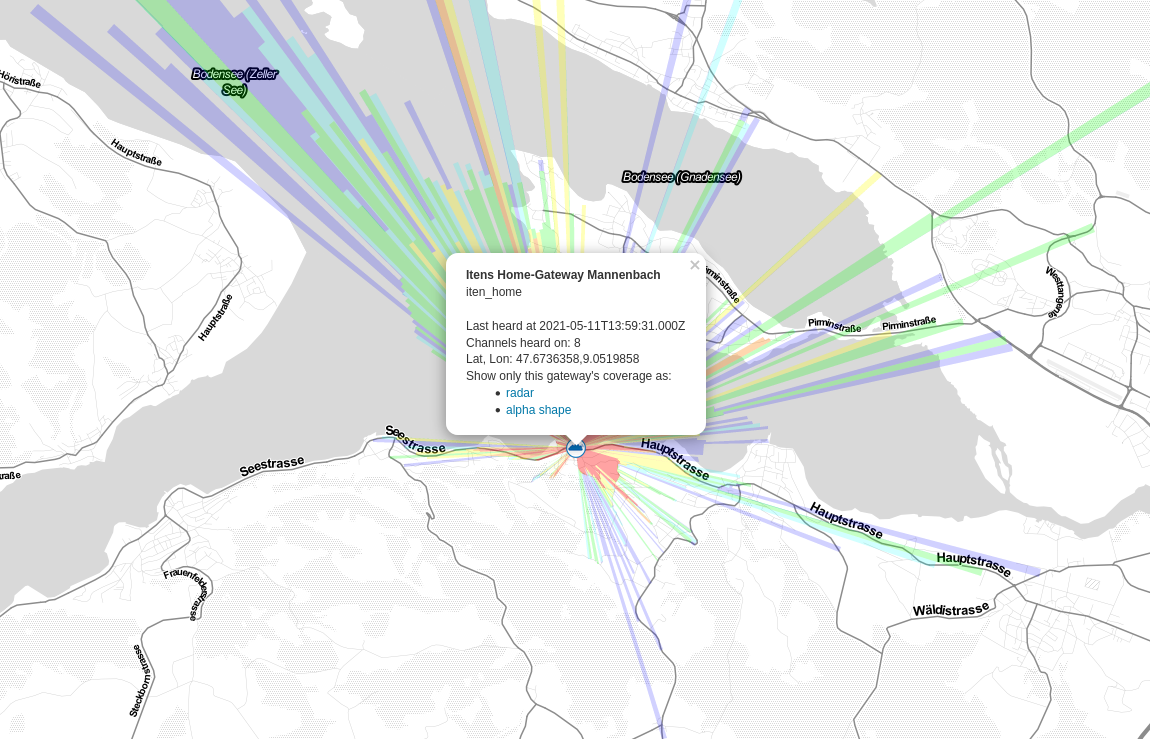
project/pictures/Range_Tests/iten_home_2.png
