norbert-walter/LoRa-Boat-Monitor/project/pictures/Range_Tests/LoRa_IJsselmeer.png

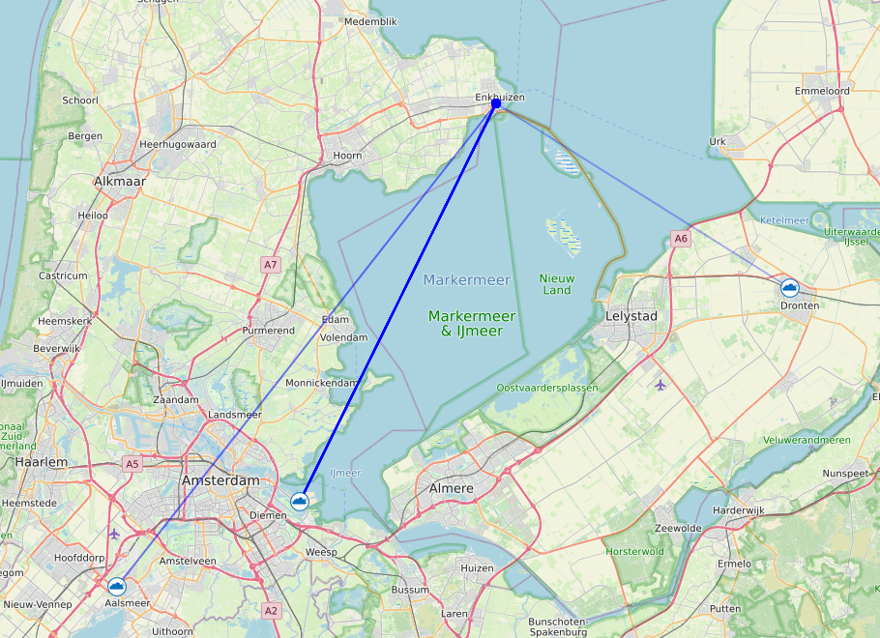
project/pictures/Range_Tests/LoRa_IJsselmeer.png
