norbert-walter/LoRa-Boat-Monitor/project/pictures/Range_Tests/LoRa_Reichweite_7.45km.jpg

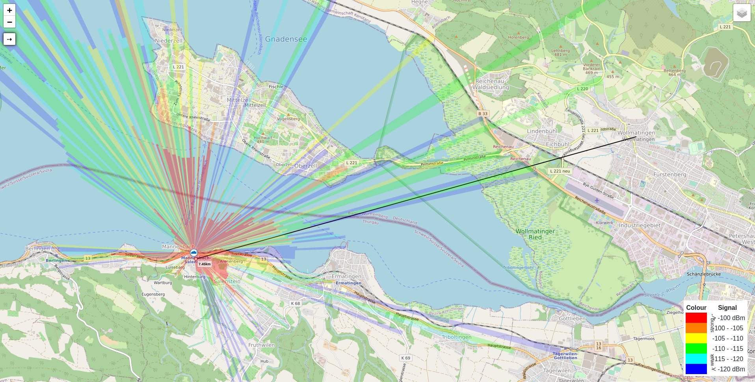
project/pictures/Range_Tests/LoRa_Reichweite_7.45km.jpg
