norbert-walter/LoRa-Boat-Monitor/project/pictures/Range_Tests/Luttelgeest-Cumulus2.png

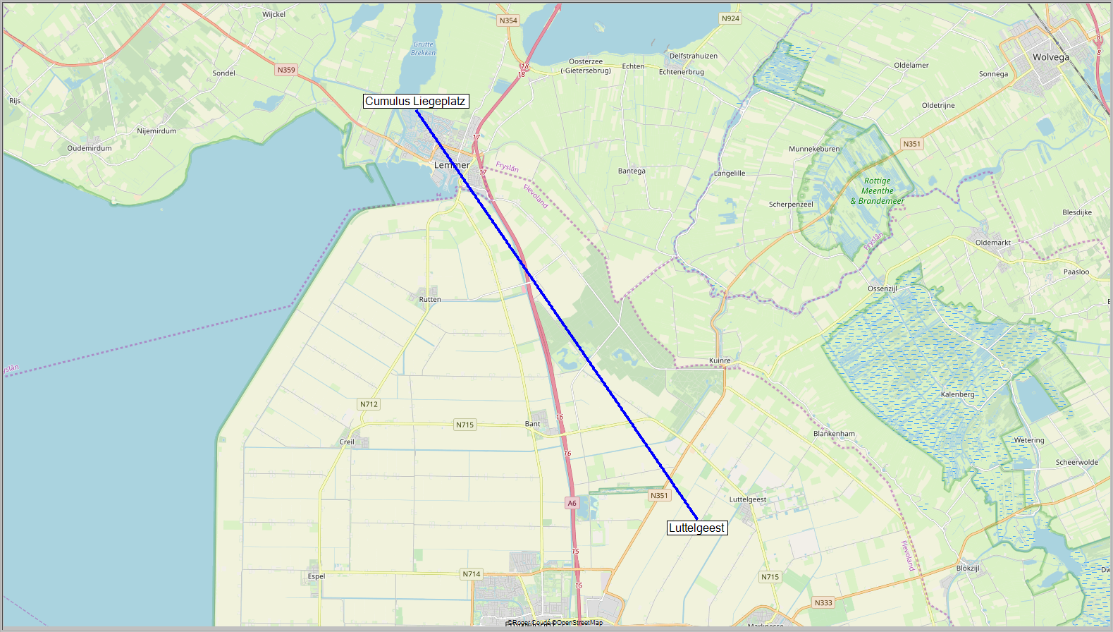
project/pictures/Range_Tests/Luttelgeest-Cumulus2.png
