norbert-walter/LoRa-Boat-Monitor/project/pictures/Range_Tests/Luttelgeest-Cumulus.png

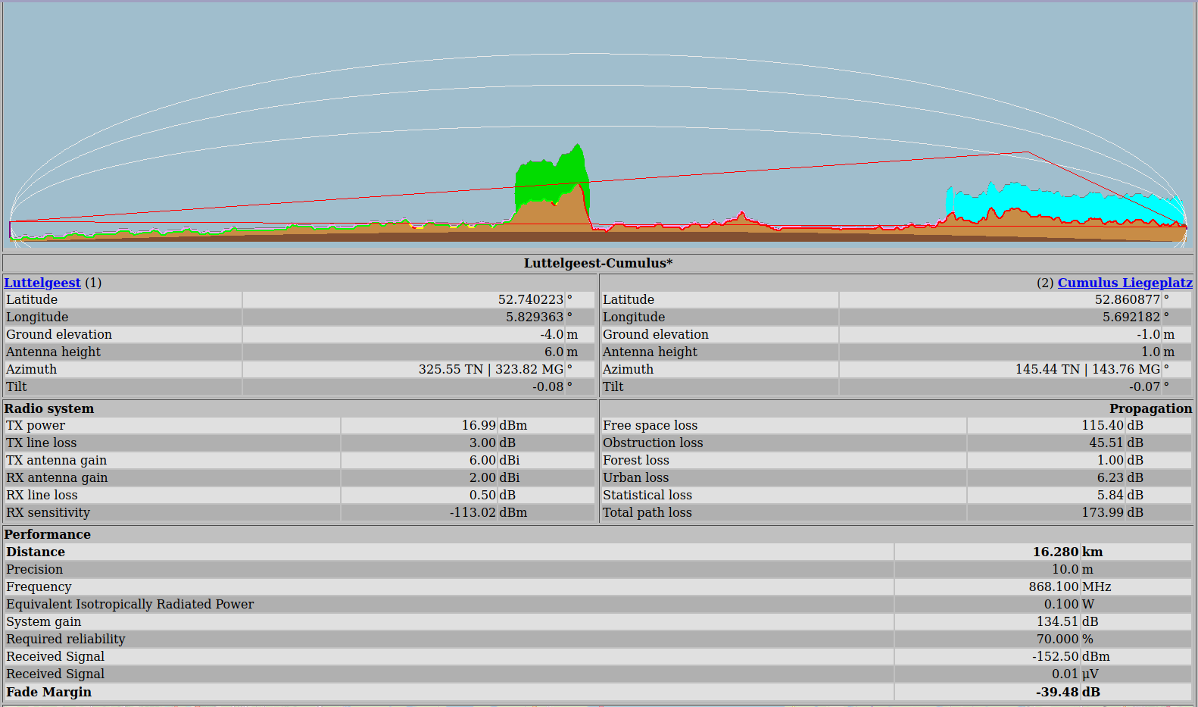
project/pictures/Range_Tests/Luttelgeest-Cumulus.png
