norbert-walter/LoRa-Boat-Monitor/project/pictures/Range_Tests/Mannebach_7.45km.jpg

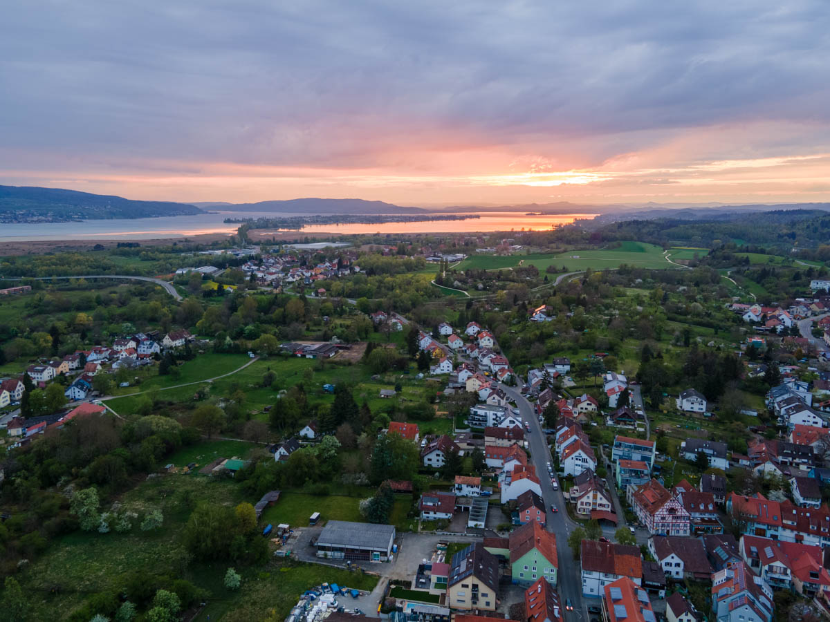
project/pictures/Range_Tests/Mannebach_7.45km.jpg
