norbert-walter/LoRa-Boat-Monitor/project/pictures/Range_Tests/Max_Reichweite.png

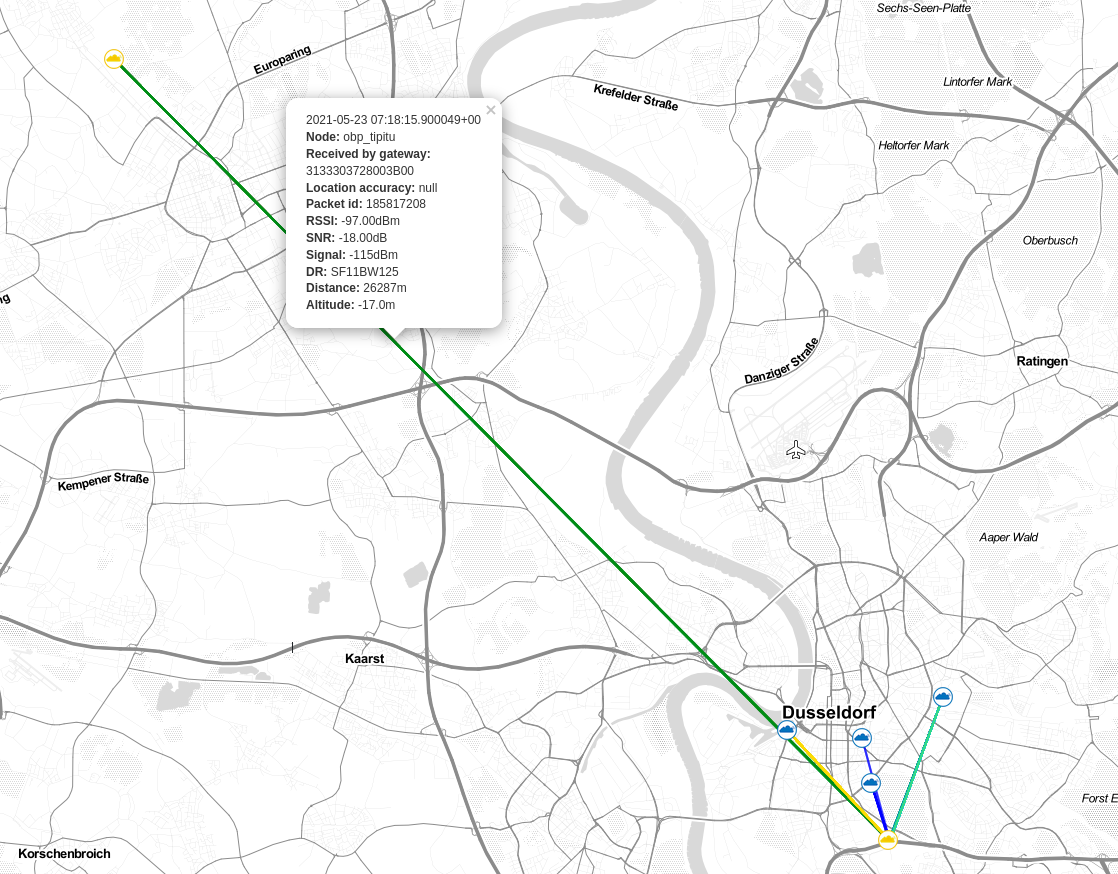
project/pictures/Range_Tests/Max_Reichweite.png
