norbert-walter/LoRa-Boat-Monitor/project/pictures/Range_Tests/Nussdorf_4.87km.jpg

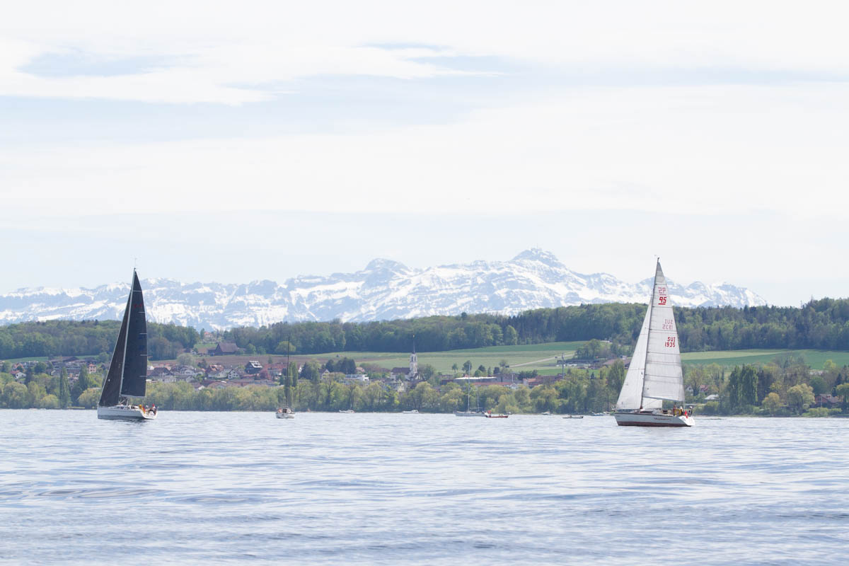
project/pictures/Range_Tests/Nussdorf_4.87km.jpg
