norbert-walter/LoRa-Boat-Monitor/project/pictures/Range_Tests/Ortsaufloesung.png

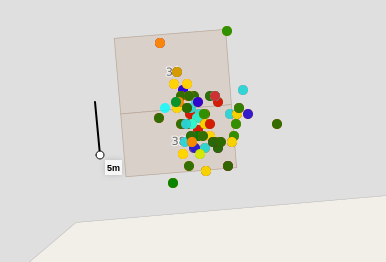
project/pictures/Range_Tests/Ortsaufloesung.png
