norbert-walter/LoRa-Boat-Monitor/project/pictures/Range_Tests/Sparrenburg.png

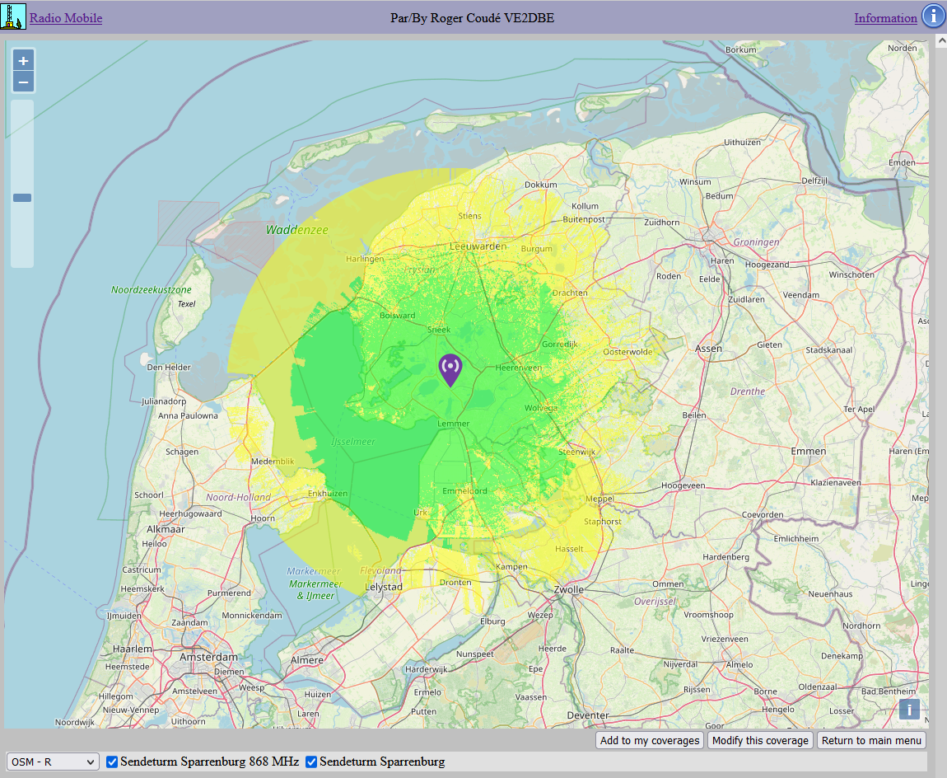
project/pictures/Range_Tests/Sparrenburg.png
