norbert-walter/LoRa-Boat-Monitor/project/pictures/Range_Tests/View_Map.png

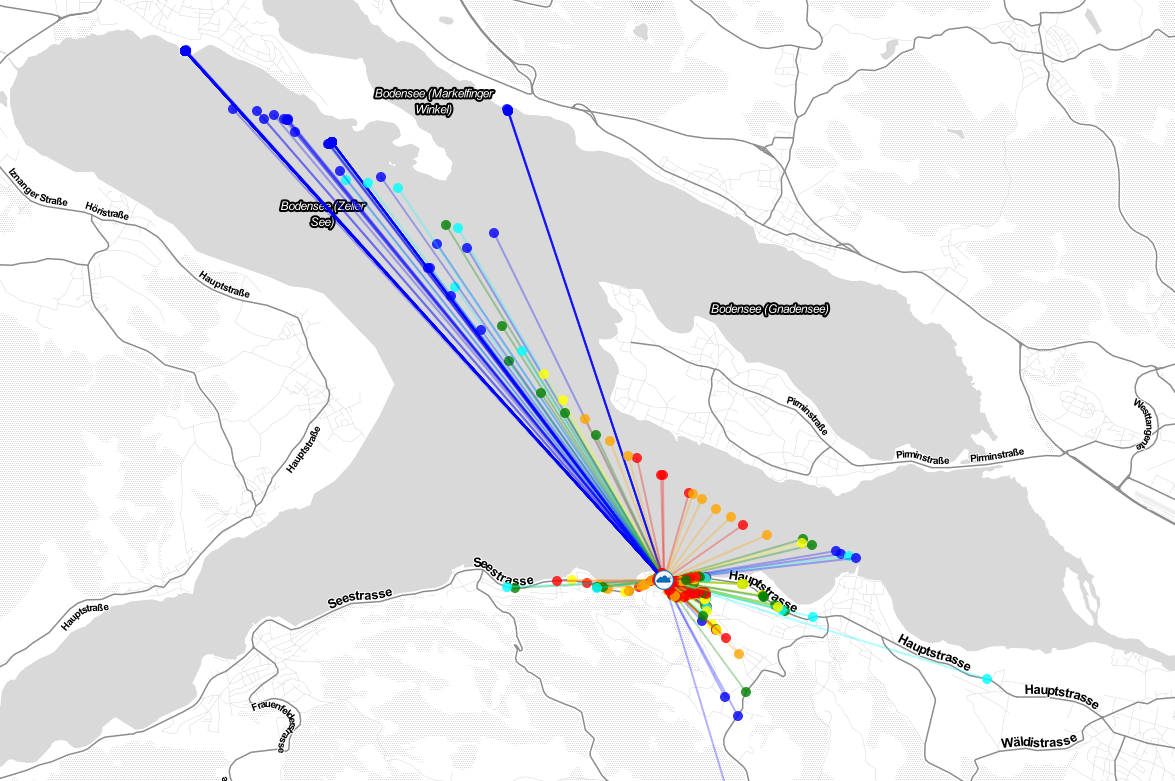
project/pictures/Range_Tests/View_Map.png
