norbert-walter/LoRa-Boat-Monitor/project/pictures/Telegram_Loss_Test/Verbindungsqualitaet.png

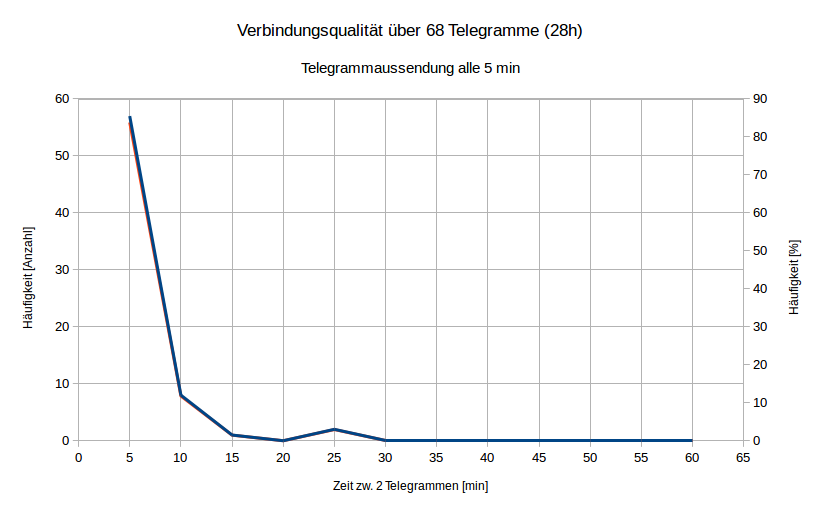
project/pictures/Telegram_Loss_Test/Verbindungsqualitaet.png
