norbert-walter/LoRa-Boat-Monitor/src/ServerPages.h

// Server pages
// Insert this library after server definition

httpServer.on("/", []() {
  // Read all received get arguments and save in a array
  int num = httpServer.args();
  String vname[num];
  String value[num];
  for (int i = 0; i < num; i++) {
    vname[i] = httpServer.argName(i);
    value[i] = httpServer.arg(i);
    // Check the return value from Restart web page
    if(vname[i] == "restart" &&  value[i] == "1"){
      resetESP = 1;
    }
    else{
      resetESP = 0;
    }
  } 
  // Send page     
  String content = Startpage(num, vname, value);
  httpServer.sendHeader("Cache-Control", "no-cache");
  httpServer.send(200, "text/html", content);

  // Restart routine
  if(resetESP == 1){
    delay(3000); // Waiting time for system restart
    resetESP = 0;
    // Restart the ESP32
    ESP.restart();
  }      
});

httpServer.on("/sensorv", []() {
  // Send page
  String content = Sensorv();
  httpServer.sendHeader("Cache-Control", "max-age=600");
  httpServer.send(200, "text/html", content);  
});

httpServer.on("/lora", []() {
  // Send page
  String content = Lora();
  httpServer.sendHeader("Cache-Control", "max-age=600");
  httpServer.send(200, "text/html", content);  
});

httpServer.on("/settings", []() {
  // Read all received get arguments and save in a array
  int num = httpServer.args();
  String vname[num];
  String value[num];
  for (int i = 0; i < num; i++) {
    vname[i] = httpServer.argName(i);
    value[i] = httpServer.arg(i);  
  } 
  // Send page
  String content = Settings(num, vname, value);
  httpServer.sendHeader("Cache-Control", "no-cache");
  httpServer.send(200, "text/html", content);  
});

httpServer.on("/restart", []() {
  // Read all received get arguments and save in a array
  int num = httpServer.args();
  String vname[num];
  String value[num];
  for (int i = 0; i < num; i++) {
    vname[i] = httpServer.argName(i);
    value[i] = httpServer.arg(i);  
  } 
  // Send page
  String content = Reset(num, vname, value);
  httpServer.sendHeader("Cache-Control", "no-cache");
  httpServer.send(200, "text/html", content);
});

httpServer.on("/firmware", []() {
  // Read all received get arguments and save in a array
  int num = httpServer.args();
  String vname[num];
  String value[num];
  for (int i = 0; i < num; i++) {
    vname[i] = httpServer.argName(i);
    value[i] = httpServer.arg(i);  
  } 
  // Send page
  String content = Firmware(num, vname, value);
  httpServer.sendHeader("Cache-Control", "no-cache");
  httpServer.send(200, "text/html", content);
});

httpServer.on("/devinfo", []() {
  String content = Devinfo();
  httpServer.sendHeader("Cache-Control", "no-cache");
  httpServer.send(200, "text/html", content);
});

httpServer.on("/favicon.ico", []() {
  String content = Icon();
  httpServer.sendHeader("Cache-Control", "max-age=600");
  httpServer.send(200, "image/svg+xml", content);
});

httpServer.on("/css", []() {
  String content = CSS();
   httpServer.sendHeader("Cache-Control", "max-age=1");
  httpServer.send(200, "text/css", content);
});

httpServer.on("/js", []() {
  String content = JS();
  httpServer.sendHeader("Cache-Control", "max-age=600");
  httpServer.send(200, "text/javascript", content);
});

httpServer.on("/json", []() {
  String content = JSON();
  httpServer.sendHeader("Access-Control-Allow-Origin", "*"); // Needs new browser for CORS (Cross Origin Resource Sharing)
  httpServer.sendHeader("Cache-Control", "no-cache");
  httpServer.send(200, "application/json", content);
});

// Use no cash because the js was permanently modifyed (transaction ID)
httpServer.on("/MD5.js", []() {
  String content = MD5();
  httpServer.sendHeader("Cache-Control", "no-cache");
  httpServer.send(200, "text/javascript", content);
});

// Firmware update
httpServer.on("/update", HTTP_POST, []() {
  httpServer.sendHeader("Connection", "close");
  httpServer.send(200, "text/plain", (Update.hasError()) ? "FAIL" : "OK");
  ESP.restart();
}, []() {
// Update routine
 HTTPUpload& upload = httpServer.upload();
    if (upload.status == UPLOAD_FILE_START) {
      Serial.printf("Update: %s\n", upload.filename.c_str());
      if (!Update.begin(UPDATE_SIZE_UNKNOWN)) { //start with max available size
        Update.printError(Serial);
      }
    } else if (upload.status == UPLOAD_FILE_WRITE) {
      /* flashing firmware to ESP*/
      if (Update.write(upload.buf, upload.currentSize) != upload.currentSize) {
        Update.printError(Serial);
      }
    } else if (upload.status == UPLOAD_FILE_END) {
      if (Update.end(true)) { //true to set the size to the current progress
        Serial.printf("Update Success: %u\nRebooting...\n", upload.totalSize);
      } else {
        Update.printError(Serial);
      }
    } 
});

httpServer.onNotFound([]() {
  String content = Error();
  httpServer.send(404, "text/html", content);
});
